mithro/esp32-to-433mhz/firmware/docs/esp32c3-cc1101-node.md

# ESP32-C3 SuperMini + CC1101 — Tasmota 433 MHz node

**Status (2026-09-05):** design + host-tested decoders + bench tooling; the
Tasmota firmware is the overlay in `firmware/` (Plan B). On-hardware validation of
the radio foundation (detect / register-I/O / selection) and the CC1101 OOK
edge-capture path is recorded in [`HWTEST-RESULTS-cc1101.md`](HWTEST-RESULTS-cc1101.md);
bench captures of the remotes/Merlin are still pending a human at the bench.

A small WiFi/USB 433 MHz transceiver: an **ESP32-C3 SuperMini** driving a
**D-SUN CC1101** SPI module (or an Ebyte E07-M1101D, or an SX1278 RA-02), running
Tasmota with a custom CC1101/SX1278 driver. It receives the Fineoffset weather
stations (FSK) — now confirmed decoding live on both a CC1101 node and the
SX1278 — and, **implemented in firmware and host-tested but not yet verified
on air**, receives the OOK-PWM remotes and the Merlin garage remote and
transmits OOK (`CcRfSend`) and Security+ 2.0. It publishes rtl_433-shaped
JSON + `RfReceived` to MQTT (and the same over its native-USB console).

> **Scope note.** The consolidated firmware in `firmware/` builds the radio
> *foundation* (detect / register-I/O / radio selection), the CC1101 OOK + FSK
> weather + decoder functionality, and the **SX1278 (RA-02) Fine Offset FSK
> receive path** (weather parity with the CC1101 — see the section below). The
> SX1278 FSK **transmit** is now implemented and **confirmed on-air** (15/15 independent
> decode at +2 dBm, see below). SX1278 OOK TX and OOK/LoRa RX are
> still future work (OOK-continuous
> RX also needs a DIO2 wire this adapter does not route); `sx1278_radio.cpp`
> currently implements only the Fine Offset FSK-RX path.

The board carrier/adapter (KiCad) and the full design spec live elsewhere: the
KiCad adapter is this repo's top-level [`README.md`](../../README.md) and
`hardware/`; the design spec and the numbered rulings (R1-R8) are in the project
repo (github.com/mithro/433mhz, `docs/.../2026-08-20-esp32c3-cc1101-tasmota-design.md`).

## Radio capability matrix

One firmware binary (`tasmota32c3-cc1101.bin`) runs on every node regardless of
which radio is fitted; `Radio auto|cc1101|sx1278` selects the active radio at
boot and the Tasmota template assigns the physical pins — there is no separate build
per radio family. (Board-type-strap auto-detection is implemented but was not exercised
on hardware; every on-hardware session used explicit `Radio cc1101`/`sx1278`.)

The two radio families are **not** at full functional parity, by design/hardware
constraint rather than by an unclosed code gap:

| Capability | CC1101 (blue E07 / green D-SUN) | SX1278 (Ra-02) |
|---|---|---|
| Fine Offset FSK RX (WS69/WH65B, WH51) | Yes | Yes — same `fineoffset_decode()` decoder as the CC1101 path |
| Fine Offset FSK RX (WS85, >=28 B frame) | **Not over-air** — the frame exceeds the CC1101's 25-byte fixed packet, so the WS85 branch is unreachable on this RX path (decoder host-tested only) | Fits the 30-byte packet (host-tested only; no WS85 sensor on air at the site) |
| OOK-PWM remote RX | Edge-capture/ISR live on hardware; a clean live OOK **remote decode** is not yet confirmed on air | **No** — OOK-continuous RX needs the SX127x **DIO2/DATA** pin, which this RA-02 adapter does not route |
| Security+ 2.0 (rolling-code garage remote) | Yes — built on the OOK-PWM RX path | **No** — depends on OOK-PWM RX, which this radio does not have on this adapter |
| OOK / Security+ 2.0 TX | Yes — template-driven pins, one firmware binary (`CcRfSend`, `SecplusSend`) | **No** — OOK TX needs the DIO2 line this adapter does not route |
| Fine Offset 2-FSK TX | No (this radio does OOK TX only) | **Yes** — `SxFskTx`, confirmed on-air (15/15 independent decode) |
| Register I/O, reset, radio selection | Yes | Yes |

**Live-hardware status (updated 2026-09-06)** (host-tested/build-verified is not the
same claim as confirmed decoding on real silicon — kept separate here):
- CC1101 blue: the OOK-PWM edge-capture path is live-verified on hardware
  (see [`HWTEST-RESULTS-cc1101.md`](HWTEST-RESULTS-cc1101.md)). green's edge-capture only
  ran via host-mediated (USB) resets; green does **not** run its app from a cold power-on
  (it boots ROM download — see the HWTEST green section), so only blue is a proven-working
  CC1101. Fine Offset FSK RX
  (WS69/WH51) is now **confirmed decoding live on CC1101 hardware** on blue,
  after the 2026-09-06 RX-bandwidth fix (MDMCFG4 `0xC9` -> `0x59`, 101 kHz ->
  325 kHz — the narrow filter could not cover the module crystal's frequency
  offset). The earlier `Decoded=0` runs predate that fix; blue's live decode, and
  the real-broker HA verification, are recorded in
  [`HWTEST-RESULTS-cc1101.md`](HWTEST-RESULTS-cc1101.md).
- SX1278 (Ra-02): Fine Offset FSK RX is both host-tested and **confirmed decoding
  live on hardware** (WS69 id 174, WH51 id 0f5d66, cross-checked against the rpi5
  reference; recorded in [`HWTEST-RESULTS-cc1101.md`](HWTEST-RESULTS-cc1101.md)).
- OOK/Security+ 2.0 TX is host-tested and build-verified but has not yet been
  exercised end-to-end against a real receiver.

[`sx1278_radio.cpp`](../src/cc1101_node/sx1278_radio.cpp) currently implements the
SX1278's Fine Offset FSK-RX path only; FSK/OOK TX, OOK-RX and LoRa are future work
(see the capability notes above).

## Wiring

The wiring diagram is generated by [`../tools/esp32c3-cc1101-node-wiring.py`](../tools/esp32c3-cc1101-node-wiring.py)
(its `WIRES` table is the single source of truth, checked by `tests/test_common.py`).

| D-SUN pin | ESP32-C3 GPIO | Role | Why |
|---|---|---|---|
| VCC | 3V3 | 3.3 V supply (~35 mA peak in TX) — **never 5 V** | SuperMini LDO is adequate |
| GND | GND | | |
| SCK | GPIO4 | SPI clock | Arduino-core FSPI default |
| MOSI (SI) | GPIO6 | SPI -> CC1101 | FSPI default |
| MISO (SO) | GPIO5 | SPI <- CC1101 (also CHIP_RDYn while CS low) | FSPI default |
| CSN | GPIO7 | chip select | FSPI default |
| GDO0 | GPIO3 | FSK: packet-ready IRQ; OOK: **TX data in** (RMT out) | no boot role |
| GDO2 | GPIO10 | OOK: **RX demod data out** (RMT capture in); FSK: spare status | no boot role |

**Do not use** GPIO2/8/9 (strapping; 8 is the blue LED, 9 is BOOT), GPIO20/21
(UART0, kept free as a fallback console), GPIO18/19 (USB D-/D+). After reset
GDO0 outputs CLK_XOSC/192 until configured — harmless on GPIO3. The D-SUN
header is 2x4; pin names as on its silkscreen: (VCC GND) (SCK MOSI) (GDO2 MISO)
(CSN GDO0). The SuperMini's PCB WiFi antenna is marginal: placement matters.

Per-board pin maps (blue E07, green D-SUN, SX1278 RA-02) that the firmware
probes at boot are tabulated in [`../README.md`](../README.md) -> *Radio
selection and SX1278 (RA-02) support*.

### Tasmota template
`GPIO4=SPI CLK, GPIO5=SPI MISO, GPIO6=SPI MOSI, GPIO7=CC1101 CS, GPIO3=CC1101 GDO0, GPIO10=CC1101 GDO2`, then `Module 0`.
See [`../README.md`](../README.md) -> *Commissioning a node* for the exact raw
`Template` array (the GDO pin functions are gated behind `USE_KEELOQ` upstream,
so only the raw array assigns them in this build).

### Reference setup on rpi5-433mhz (direct SPI, no ESP)

| D-SUN | Pi 5 header | BCM |
|---|---|---|
| VCC | pin 1 | 3V3 |
| GND | pin 6 | GND |
| SCK | pin 23 | GPIO11 SCLK |
| MOSI | pin 19 | GPIO10 MOSI |
| MISO | pin 21 | GPIO9 MISO |
| CSN | pin 24 | GPIO8 CE0 (`/dev/spidev0.0`) |
| GDO2 | pin 18 | GPIO24 — **black** wire (OOK capture, [`../tools/cc1101_ook_capture.py`](../tools/cc1101_ook_capture.py) `--gpio 24`) |
| GDO0 | pin 22 | GPIO25 — **green** wire (reserved for async TX tests) |

GDO assignment measured 2026-08-22 with [`../tools/cc1101_find_gdo_pins.py`](../tools/cc1101_find_gdo_pins.py)
(drives each GDO to a fixed level and scans the header: `GDO2 -> GPIO24 (header
pin 18)`, `GDO0 -> GPIO25 (header pin 22)`); wire colours as recorded by Tim.
The 3V3/GND pin numbers are the conventional choice, not measured. The Pi-side
reference driver is [`../tools/cc1101.py`](../tools/cc1101.py), which the firmware
presets are proven against (`tests/test_presets.py`).

## Bill of materials (9 units)
ESP32-C3 SuperMini x9 · D-SUN CC1101 433 MHz module with antenna x9 ·
8-way female-female jumper sets or a 2x4 + 2x8 header adapter x9 · USB-C cable
and 5 V supply per deployed node.

## Modes, commands, MQTT

All commands are issued on the Tasmota console or over MQTT as
`cmnd/<topic>/<Command> [args]`, replying on `stat/<topic>/RESULT`. Config-setting
commands persist to `/cc1101.cfg`. For the full per-field MQTT message schema, the
Home Assistant autodiscovery setup (the `rtl433-mqtt-autodiscovery` add-on on
`rtl_433/+/events`), the `CcHass` events-topic option, node MQTT configuration and
the live-broker validation procedure, see
[`mqtt-home-assistant.md`](mqtt-home-assistant.md).

### Command reference

**Radio selection and mode**

| Command | Args | Description |
|---|---|---|
| `Radio` | `auto\|cc1101\|sx1278` | Select and persist the active radio engine; re-runs bring-up. |
| `CcMode` | `weather\|remotes` | CC1101 role: Fine Offset FSK RX (`weather`) or OOK-PWM remotes RX (`remotes`). Persisted. |

**CC1101**

| Command | Args | Description |
|---|---|---|
| `CcStatus` | - | Present, PARTNUM/VERSION/MARCSTATE, mode/preset, RSSI, Rx/Decoded/Tx/Overflow counters. |
| `CcPreset` | `<name>` | Load a named preset and enter RX (debug). |
| `CcReg` | `<addr> [val]` | Read/write a CC1101 register (0x00-0x3F; writing 0x30-0x3D issues a strobe). |
| `CcRaw` | `0\|1` | Publish drained-but-undecodable frames as hex on `tele/<topic>/CCRAW`. |
| `CcHass` | `0\|1` | Events topic layout: `0` = `rtl_433/nodes/<host>/events` (aggregator), `1` = `rtl_433/<host>/events` (direct HA autodiscovery). |
| `CcRfSend` | `{"Data","Bits","Protocol":1,"Pulse","Repeat"}` | Transmit an OOK-PWM (RCSwitch protocol 1) code. |
| `CcTxPower` | `[byte]` | CC1101 OOK **mark** level = `PATABLE[1]` (`0` = preset default; e.g. `0xC0` ~ +10 dBm at 433 MHz). Space stays `PATABLE[0]=0x00`. |
| `CcRxGain` | `[byte]` | CC1101 `AGCCTRL2` (0x1B) RX-gain override (`0` = preset default; lower `MAX_LNA/DVGA_GAIN` reduces sensitivity for a strong co-located source). |

**SX1278 (RA-02)**

| Command | Args | Description |
|---|---|---|
| `SxStatus` | - | Present, VERSION, Active, Mode, WeatherRx, RSSI, Rx/Decoded/Tx. |
| `SxReg` | `<addr> [val]` | Read/write an SX127x register (address bit7 = write). SX1278 must be the active radio. |
| `SxReset` | - | Hardware reset (RST pulse) and re-identify. |
| `SxFskTx` | `<hex>` | Transmit the hex payload as a fixed-length 2-FSK packet matched to the RX preset (433.92 MHz, 17.241 kbps, sync 0x2DD4). |
| `SxTxPower` | `[2..17]` | SX1278 PA_BOOST output power in dBm (`0` = default +17). |
| `SxRxGain` | `[1..6]` | SX1278 LNA gain (`1` = max G1 .. `6` = min G6; `0` = AGC-auto default). |

**Security+ 2.0** (CC1101 only)

| Command | Args | Description |
|---|---|---|
| `SecplusId` | `[id]` | Get/set the persisted Security+ 2.0 device id. |
| `SecplusCounter` | `[n]` | Get/set the rolling counter (persisted before each keying). |
| `SecplusFreq` | `[f1 f2 f3]` | Get/set the frequency legs (default 433.92). |
| `SecplusSend` | - | Transmit a Security+ 2.0 rolling-code frame. |

> Note: `SxFskTx` and `SxTxPower`/`SxRxGain` (and the CC1101 `CcTxPower`/`CcRxGain`)
> are the runtime power/TX controls added for co-located on-air testing -- reduce
> TX power (or RX gain) so a nearby receiver is not desensitised.

## Decoders and fixtures (host-tested)
`../decoders/` — Fineoffset WS69/WH65B/WS85/**WH51** (soil moisture, family 0x51) and OOK-PWM in pure C, tested with
`uv run --with pytest pytest firmware/tests` against real captures in
`../fixtures/`. rtl_433 field names throughout. The bit-sense convention of the
OOK-PWM codes is documented in the project repo's `protocols/ook-pwm-remotes.md`.

## Fine Offset FSK RX configuration and packet-length handling

The `fineoffset-fsk` preset (`../src/cc1101_node/cc1101_presets.c`) programs the
CC1101 like the bench-proven reference `cc1101_watch.py`
(`configure_fineoffset_fsk_rx`), computed from the datasheet formulas, with one
deliberate deviation: the RX bandwidth is widened from the reference's 101 kHz to
**325 kHz** (MDMCFG4 `0xC9` -> `0x59`) so the filter covers the module crystal's
frequency offset (2026-09-06 fix; see `cc1101_presets.c`). Every other register
was read back from a live node (`CcReg`) and matches the reference:

| Purpose | Register(s) | Value |
|---|---|---|
| Carrier 433.92 MHz | FREQ2/1/0 (0x0D/0E/0F) | `10 B0 71` |
| Bit rate 17.24 kbps | MDMCFG4/3 (0x10/0x11) | `59 5C` |
| 2-FSK, 16/16 sync, no Manchester | MDMCFG2 (0x12) | `02` |
| 24-byte preamble | MDMCFG1 (0x13) | `72` |
| Deviation 50 kHz | DEVIATN (0x15) | `50` |
| Sync word 0x2DD4 | SYNC1/0 (0x04/0x05) | `2D D4` |
| Fixed length, APPEND_STATUS, no CRC autoflush | PKTCTRL0/1 (0x08/0x07) | `00` / `04` |
| Channel BW 325 kHz | (in MDMCFG4) | — |

**Packet length — receiving both WS69 (25 B) and WH51 (14 B).** The CC1101 runs a
fixed-length packet (`CC_FSK_PKTLEN = 25`, sized to the WS69/WH65B frame, whose
tail CRC needs all 25 bytes). `CcWeatherPoll()` accepts a *range* of Fine Offset
frame lengths so the shorter WH51 is also captured and dispatched:

- **Full-packet path** (`RXBYTES >= PKTLEN + 2`): reads the completed 25-byte
  packet plus its 2 appended status bytes and calls `fineoffset_decode()`, which
  dispatches by the family byte — `0x24` -> WS69/WH65B, `0x51` -> WH51,
  `0x85` -> WS85. A 14-byte WH51 arrives in the first 14 bytes with the rest of
  the packet filled by demodulated bytes; the decoder ignores everything past the
  14-byte frame (validated by CRC-8 poly 0x31 + additive checksum), so it decodes
  correctly inside the longer read.
- **Short-frame rescue** (`RXBYTES >= 14` and the FIFO has stopped growing):
  drains a WH51 whose packet stalled before completing 25 bytes, and decodes it
  **only when it starts with the WH51 family byte 0x51** — so a partially-filled
  WS69/WS85 (both arrive in one <=12 ms burst, faster than the 50 ms poll) can
  never be truncated into a false decode.

**WS85 is not audible at Welland.** A WS85 frame is >=28 bytes — longer than the
fixed 25-byte packet — so its decode branch is unreachable on this RX path and no
WS85 was heard on air during the 2026-09-05 survey. WS85 (family 0x85) is
therefore validated by the decoder host test (real rtl_433 doc vector) only — Renode's
cc1101_decode suite runs WS69+WH51, not WS85 — and not by a live capture. Raising `CC_FSK_PKTLEN` to fit WS85 would stop the CC1101
completing the shorter WS69 frame, so it is left at 25.

## SX1278 (RA-02) Fine Offset FSK RX configuration

The SX1278 receives the same Fine Offset families as the CC1101 weather path
(`../src/cc1101_node/sx1278_radio.cpp`, `configure_fineoffset_fsk()`). Every value
is computed from the SX1276/78 datasheet formulas and matched to the bench-proven
SX1276 receiver at the same Welland site (rpi5 `~/wh51-watch`, RadioLib
`beginFSK`: 433.92 MHz, 17.241 kbps, ~50 kHz fdev, sync `0x2DD4`, 2-FSK with
`ModulationShaping = NONE`):

| Purpose | Register(s) | Value |
|---|---|---|
| FSK mode (LongRangeMode=0), low-freq band, RX | RegOpMode (0x01) | `0D` |
| Carrier 433.92 MHz (`Frf = Fstep·RegFrf`, Fstep = 32 MHz/2¹⁹) | RegFrf (0x06/07/08) | `6C 7A E1` |
| Bit rate 17.241 kbps (`FXOSC / RegBitrate`) | RegBitrate (0x02/03) | `07 40` |
| Deviation ~50 kHz (`Fstep · RegFdev`) | RegFdev (0x04/05) | `03 33` |
| RX bandwidth 125 kHz (mant=16, exp=2) | RegRxBw (0x12) | `02` |
| AGC auto + RX trigger on preamble detect | RegRxConfig (0x0D) | `0E` |
| Preamble detector on, 2 bytes, tol 10 | RegPreambleDetect (0x1F) | `AA` |
| AutoRestartRx + SyncOn + 2 sync bytes (0xAA preamble polarity) | RegSyncConfig (0x27) | `91` |
| Sync word 0x2DD4 | RegSyncValue1/2 (0x28/29) | `2D D4` |
| Fixed length, no DC-free, no CRC, no addr filter | RegPacketConfig1 (0x30) | `00` |
| Packet (not continuous) data mode | RegPacketConfig2 (0x31) | `40` |
| Fixed payload length = `SX_FSK_RX_LEN` (30) | RegPayloadLength (0x32) | `1E` |
| DIO0 = PayloadReady (also polled via RegIrqFlags2) | RegDioMapping1 (0x40) | `00` |

**Packet length — one config for every family.** Unlike the CC1101's 25-byte
fixed packet + short-frame rescue, the SX1278 runs **fixed-length packet mode with
`RegPayloadLength = SX_FSK_RX_LEN = 30`** — chosen `>=` the longest WS85 frame
(28 B) yet `<=` the 64-byte FIFO. After the demodulator matches `0x2DD4`, the radio
latches 30 bytes into the FIFO and raises **PayloadReady**; `sx_weather_drain()`
(`../src/cc1101_node/sx1278_weather.cpp`) reads all 30 out of `RegFifo` and
`fineoffset_decode()` dispatches by family byte (`0x24` WS69/WH65B, `0x51` WH51,
`0x85` WS85), ignoring the trailing demodulator noise that follows a short frame.
So **one** setting receives WH51 (14 B), WS69 (25 B) and WS85 (28 B) — the SX1278
does not need the CC1101's split full-packet/short-frame logic because 30 bytes
always fits every family and the decoder self-selects by length. Because 30 <= 64
the frame never straddles a FIFO refill. After each drain the driver does a
`standby -> RX` (`restart_rx()`) — belt-and-suspenders alongside AutoRestartRx —
to flush the FIFO and re-arm sync detection.

`SX_FSK_MIN_FRAME` is 14 (WH51); anything the decoder rejects is optionally
published as raw hex over `tele/…/CCRAW` when `CcRaw 1` is set. The SX1278 does
**weather RX only**: OOK-continuous "remotes" RX needs the SX127x DIO2 data line,
which this RA-02 adapter does not route, so `CcMode remotes` leaves the SX1278 in
standby.

Host-tested end to end by `../tests/test_sx1278_weather_rx.py`, which drives the
identical `sx_weather_drain()` through a scripted FIFO for WH51/WS69/WS85 and
asserts the config registers above against the datasheet math.

## SX1278 (RA-02) Fine Offset FSK transmit

`SxFskTx <hex>` transmits the payload as a fixed-length 2-FSK packet through the SX1278 (which
must be the active radio, `Radio sx1278`). The TX preset (`configure_fsk_tx()`) uses the
**same** carrier / bit-rate / deviation / sync as the RX preset (433.92 MHz, 17.241 kbps,
~50 kHz fdev, 0xAA preamble + 0x2DD4 sync), so a peer running the CC1101 `FINEOFFSET_FSK`
preset -- or another SX1278 in weather RX -- is on-air compatible. The command pauses weather
RX, loads the FIFO, keys the transmitter (PA_BOOST, +17 dBm), waits for the `PacketSent` IRQ
(with a timeout), then re-arms RX; `SxStatus` reports a `Tx` counter.

**OOK TX is not provided:** like OOK RX, arbitrary OOK-PWM transmit needs the SX127x
continuous-mode DATA line (DIO2), which the RA-02 socket does not route (`SX_MAP_RA02` wires
only DIO0). FSK *packet* TX drives the FIFO over SPI and works on the wiring as built.

**Validation state (2026-09-08):** host-tested (SPI framing, FIFO burst-write order, and TX
modem params asserted equal to the RX preset -- `../tests/test_sx1278_fake_bus.py`) **and
confirmed on-air.** The transmit was received and decoded by an INDEPENDENT receiver -- the
rpi5-SPI CC1101 (`~/wh51-watch/cc1101_watch.py`, a different chip and a different decoder
codebase than this firmware): a 15-frame burst of the WH51 fixture at **+2 dBm** (`SxTxPower 2`)
produced 15/15 decodes of id `0f5c54` at RSSI -41 dBm (vs the real sensor's -73..-88 dBm; a
rapid cluster impossible for the ~70 s-interval real sensor). At the default +17 dBm the
co-located receiver was desensitised and decoded nothing -- the runtime `SxTxPower` control
(and `CcTxPower`/`SxRxGain`/`CcRxGain`) exists precisely for co-located on-air tests. This is
both an on-air TX confirmation and an independent-oracle cross-check of the node's output.

## Why these choices (so they aren't relitigated)
- **Why RMT:** the C3's RMT peripheral timestamps edges in hardware (1 us) and
  buffers them; WiFi/MQTT cannot jitter pulse measurement; the same peripheral
  generates exact TX pulse trains, which Security+ 2.0 needs.
- **Why two GDOs:** packet mode (FSK) wants an IRQ on GDO0; async-serial mode
  (OOK) wants RX data on GDO2 and TX data on GDO0. The D-SUN has both.
- **Why not ESPHome/Berry:** estate and HA are Tasmota; stock Tasmota has no
  CC1101 driver and Berry has no SPI/RMT — see the design spec section 2.
- **FSK vs OOK exclusivity:** a CC1101 does one at a time; nodes get a role
  (`CcMode weather|remotes`).

## Verification log
| Date | Check | Result (command output) |
|---|---|---|
| 2026-08-20 | WS69 id 174 25-byte frames on Pi CC1101 (`cc1101_ws69_rx.py --packet-len 25`) | `24 AE 5D 82 13 52 05 01 07 24 00 00 00 00 00 5A A1 01 FF FF FF 01 6B 87 33` twice at 16 s, RSSI -85.5/-87.0 dBm; both CRCs valid; decodes 13.1 C 82 % 349 deg 464.3 mm |
| 2026-08-22 | async-OOK capture path: GDO2->GPIO24 (measured with `cc1101_find_gdo_pins.py`); no-remote baseline — `MARCSTATE=0x0D`, `edges=48 trains(>=16 pulses)=0` over 10 s — path live end-to-end. Remote captures vs the codes doc, and rtl_433 cross-check: **PENDING — needs a human at the Welland bench** |
| 2026-09-05 | Tasmota firmware on real CC1101 (blue E07 + green D-SUN), native-USB console: PARTNUM 0x00 / VERSION 0x14, register I/O, radio selection, OOK edge-capture live; SX1278 RA-02 RegVersion 0x12 detect + register-I/O + selection | See [`HWTEST-RESULTS-cc1101.md`](HWTEST-RESULTS-cc1101.md) |
| 2026-09-05 | WH51 decoder: real frame `51 0F 5C 54 10 7F 28 F8 D0 FF FF FF 4B D7` (id 0f5c54) captured by the rpi5 reference logger; host test asserts moisture 40, battery 1600 mV, ad_raw 208, battery_ok 1.0 vs rtl_433 -> **108 host tests pass** (as of this 2026-09-05 entry; the suite is now 146 tests) | `pytest firmware/tests` |
| 2026-09-05 | WH51 live on a node CC1101: **NOT decoded.** blue (E07) + green (D-SUN) in `weather` mode received strong 433.92 FSK traffic (RSSI down to -26 dBm) and completed packets (`Rx` climbing), but never a WH51 frame (`Decoded=0`); registers directly comparable to the proven reference read back identical, PKTLEN 25->17 tried, sync relaxed 16/16->15/16 (`Rx` 376 in 90 s, still `Decoded=0`). The reference CC1101/LilyGo on rpi5 heard the same WH51 sensors at -74..-82 dBm throughout. Cause not isolated in this run (a packet-framing config bug — fixed-length vs. infinite-length mode — was found afterward; whether that explains this result is unproven on this hardware, since PKTLEN=17 was also tried here and still did not decode). **Superseded (2026-09-06):** the cause was RX bandwidth — MDMCFG4 `0xC9` (101 kHz) is too narrow for the module crystal's frequency offset; widening it to `0x59` (325 kHz) made blue decode WS69+WH51 live (recorded in the on-hardware results log). | reference `cc1101.hits.jsonl` vs node console |
| 2026-09-05 | **SX1278 (RA-02) FSK weather RX — LIVE, decoded.** Node MAC 44:1B:F6:2E:B3:80 (`/dev/radio-sx1278-ra02`) flashed with this build, `Radio sx1278` + `CcMode weather`: `SxStatus` -> `Present 1, VERSION 0x12, WeatherRx 1`; console `RSL: events` lines decoded **WS69 id=174** (humidity 79, `mic:CRC`) repeatedly at RSSI -89..-93 dBm and **WH51 id=0f5d66** (moisture 38, `mic:CRC`), i.e. both families through the single fixed-length FSK config. Cross-checked against the rpi5 reference (`~/wh51-watch`) for the same window: reference heard WS69 family 0x24 id 0xAE(174) humidity 0x4F(79) and WH51 id 0f5c54 valid at -82 dBm. Float fields render as `*float*` on-target (shared-decoder `%f` under newlib-nano, affects the CC1101 path identically — not radio-specific; integer fields + CRC MIC correct). | node console vs `cc1101.hits.jsonl`/`lilygo.jsonl` |
| 2026-08-22 | Merlin remote: rtl_433 -R 164 / 178 / -A | **PENDING — needs a human to press the remote**; procedure in the project repo's `protocols/secplus-v2.md` |
| 2026-09-05 | **FIX-A: SX1278 (RA-02) re-capture with the `rf_ftoa` float fix (`4c85365`), valid floats confirmed + 3-way cross-check.** Single reflash from HEAD `cd95b48` (`firmware/dist/tasmota32c3-cc1101.factory.bin`, sha256 `9c933635b5...`), `esptool write_flash 0x0`, hash-verified; commissioned `Radio sx1278` (weather RX already persisted from the WAVE A2 session). 10-minute passive console capture over a persistent `dtr=False,rts=False` connection, 2026-09-05T12:53:39-13:03:39 UTC. `events` JSON now carries real numeric floats end to end, e.g. `{"model":"Fineoffset-WS69","id":174,"battery_ok":1,"temperature_C":13.0,"humidity":84,"wind_dir_deg":8,"wind_avg_m_s":0.4,"wind_max_m_s":0.5,"rain_mm":517.7,"uv":0,"uvi":0,"light_lux":0.0,"mic":"CRC"}` and `{"model":"Fineoffset-WH51","id":"0f5c54","battery_ok":1.0,"battery_mV":1600,"moisture":40,"boost":0,"ad_raw":208,"mic":"CRC"}` - **no `*float*` anywhere in the 10-minute capture** (previously reported bug from WAVE A2 is fixed). **Cross-check:** (1) WH51 **target id `0f5c54`** (previously below the CC1101-node SNR budget) decoded by the node at 13:03:36.354 UTC matches, byte-for-byte on the 14-byte payload (`51 0F 5C 54 10 7F 28 F8 D0 FF FF FF 4B D7`), the rpi5 reference CC1101 logger (`cc1101.hits.jsonl`, ts 13:03:36.048) **and** the LilyGo SX1276 logger (`lilygo.hits.jsonl`, ts 13:03:36.053) - moisture 40, battery 1600 mV, ad_raw 208 on all three receivers. (2) WS69 id=174 events at 12:53:59.446/12:54:31.279 UTC match the LilyGo raw frames (`24 AE 08 ...`/`24 AE 0B ...`) byte-for-byte on the shared payload, decoding to identical temperature_C 13.0, humidity 84, wind_dir_deg 8, wind_avg_m_s 0.4, wind_max_m_s 0.5, rain_mm 517.7. (3) Pluto SDR (`rpi-sdr-pluto`, `rtl_433 -d driver=plutosdr`): its pre-existing continuous logger (running unattended since 2026-09-02) had already stopped producing new decodes before this session started (last flush recorded, per its own drifting internal clock, `"time":"2026-09-05T13:44:32"`, `rain_mm:517.144` = 2 tip-counts / 0.5 mm behind the node/reference's `517.7`, i.e. genuinely stale, not futuristic) - it continues to independently confirm the same on-air WS69 id=174 (same battery_ok, same rain-counter epoch) but not from inside this session's exact 10-minute window. Two restarts (its own auto-restart wrapper) reconnected to the Pluto cleanly (no USB claim errors) but did not resume live decoding within this session's time budget - an infra/logging-tool staleness issue on a *pre-existing, unattended* capture tool, not a fault in the node/firmware under test or in the Pluto radio itself. **Node stayed healthy** throughout (single flash, no further reflash); one console reconnect for a post-capture `SxStatus` check reset the RAM counters only (config/mode persisted) - the same known reconnect-resets-C3 bench-harness gotcha already documented above. | node console (`a2recap-node-console.log`) vs `cc1101.hits.jsonl`/`lilygo.hits.jsonl`/pluto `rtl433.jsonl` |

## See also
- [`../README.md`](../README.md) — firmware build, flashing, commissioning, command reference, MQTT.
- [`../RECOVERY.md`](../RECOVERY.md) — reflashing a bricked/misbehaving board, restoring `/cc1101.cfg`.
- [`HWTEST-RESULTS-cc1101.md`](HWTEST-RESULTS-cc1101.md) — on-hardware validation log.
