mithro/esp32-to-433mhz/hardware/parts/sx1278-ra02-breakout/photos/ra02-header.jpg

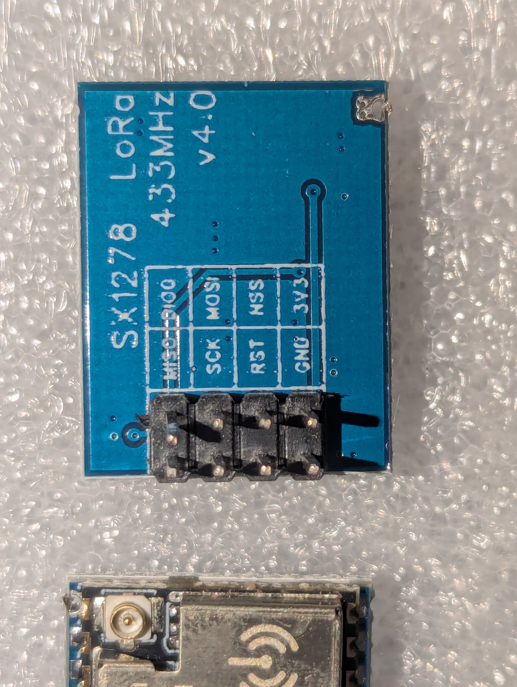
hardware/parts/sx1278-ra02-breakout/photos/ra02-header.jpg
