mithro/esp32-to-433mhz/hardware/3d/cc1101-dsun.step

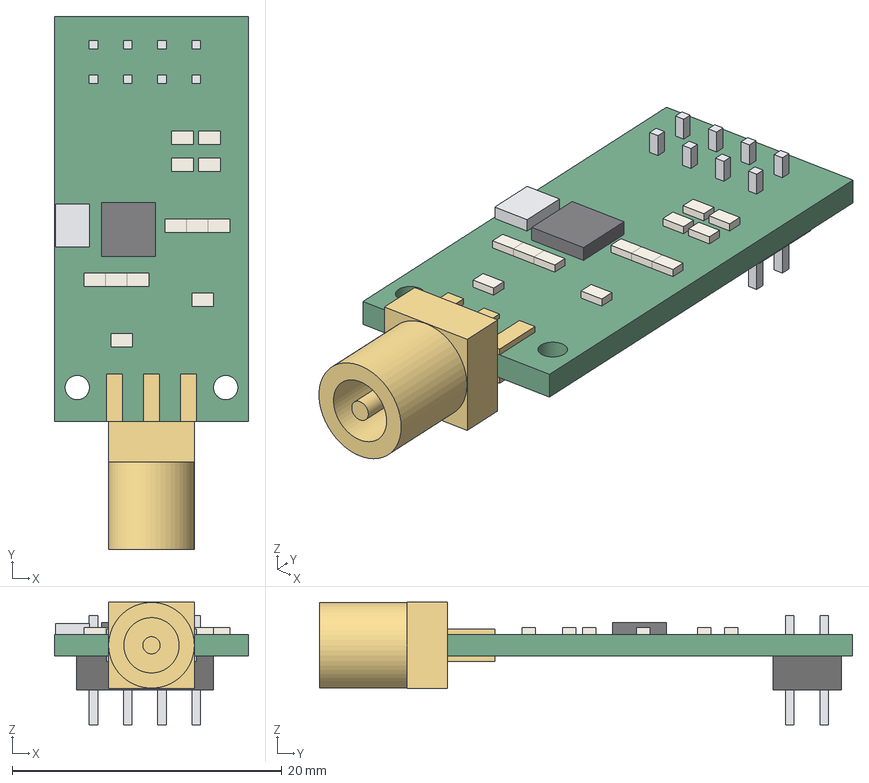
[picture p60: CAD file, 2026-09-10]
hardware/3d/cc1101-dsun.step
14.4 x 39.5 x 9.10 mm
pcb_0
cc1101_1
crystal_2
passive_3
passive_4
passive_5
passive_6
passive_7
passive_8
passive_9
passive_10
passive_11
passive_12
passive_13
passive_14
sma_body_15
sma_pin_16
sma_leg_17
sma_leg_18
sma_leg_19
sma_leg_20
sma_leg_21
pins_23
