mithro/esp32-to-433mhz/hardware/3d/esp32-c3-supermini-components.step

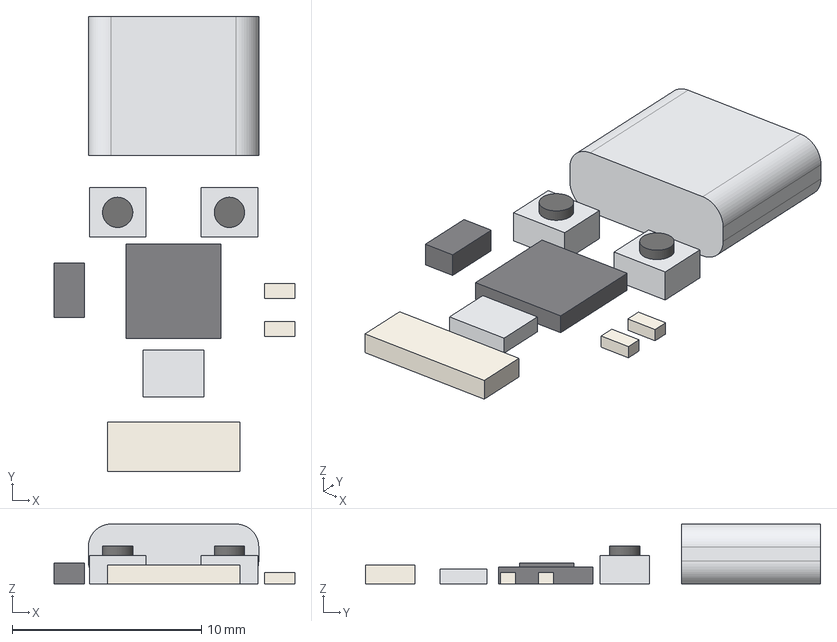
[picture p61: CAD file, 2026-09-10]
hardware/3d/esp32-c3-supermini-components.step
12.7 x 24.0 x 3.16 mm
usb_c_0
button_1
button_cap_2
button_3
button_cap_4
esp32c3_5
crystal_6
ldo_7
led_8
led_9
antenna_10
