mithro/esp32-to-433mhz/hardware/3d/cc1101-dsun-components.step

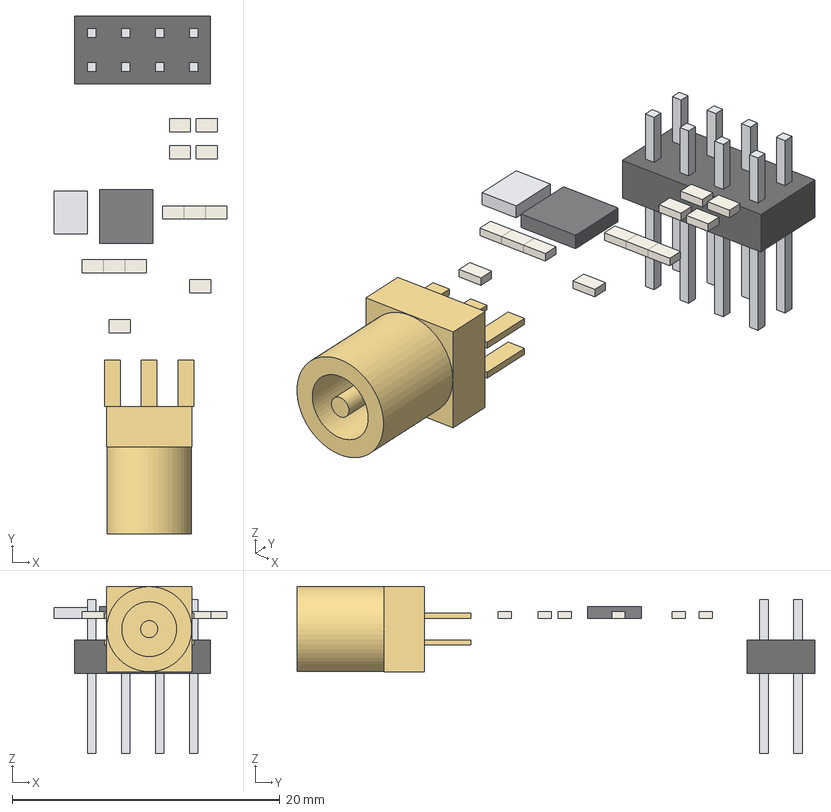
[picture p62: CAD file, 2026-09-10]
hardware/3d/cc1101-dsun-components.step
12.9 x 38.7 x 12.5 mm
cc1101_0
crystal_1
passive_2
passive_3
passive_4
passive_5
passive_6
passive_7
passive_8
passive_9
passive_10
passive_11
passive_12
passive_13
sma_body_14
sma_pin_15
sma_leg_16
sma_leg_17
sma_leg_18
sma_leg_19
sma_leg_20
pins_22
