mithro/esp32-to-433mhz/hardware/3d/sx1278-ra02-pigtail.step

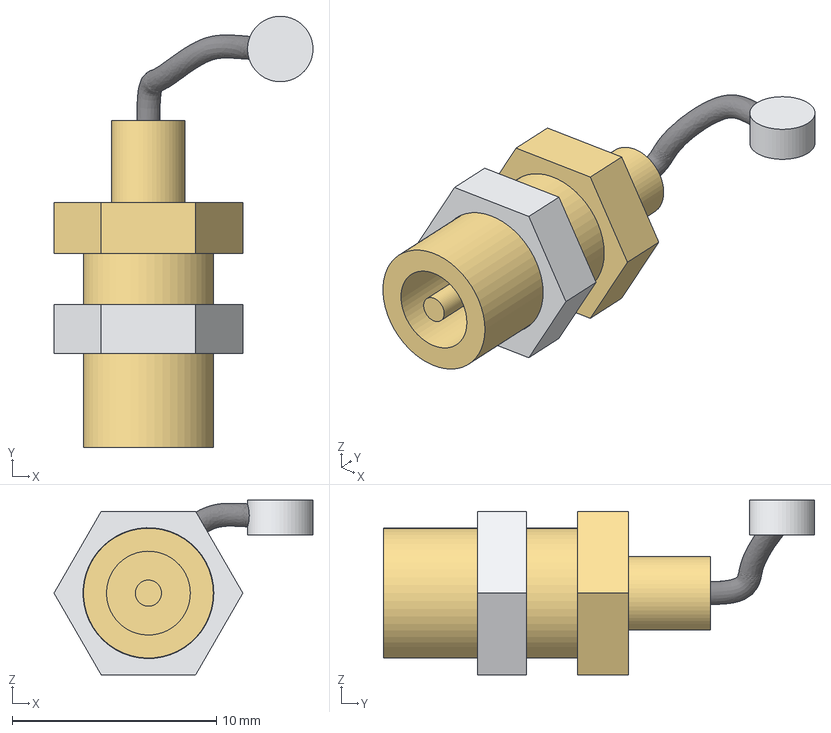
[picture p63: CAD file, 2026-09-10]
hardware/3d/sx1278-ra02-pigtail.step
12.7 x 21.1 x 8.55 mm
ufl_plug_0
cable_1
sma_bulkhead_2
sma_pin_3
sma_nut_4
