mithro/esp32-to-433mhz/docs/images/esp32c3-radio-adapter-assembly-e07-top.png

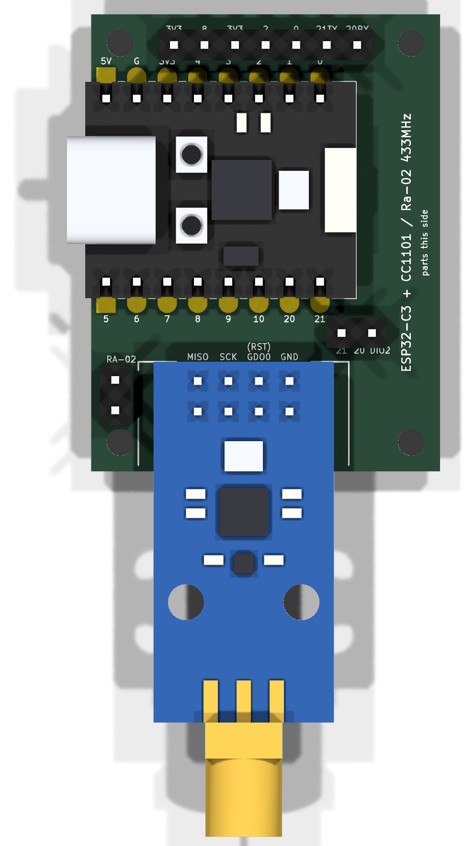
docs/images/esp32c3-radio-adapter-assembly-e07-top.png
