mithro/esp32-to-433mhz/docs/images/esp32c3-sx1278-adapter-assembly-module-top.png

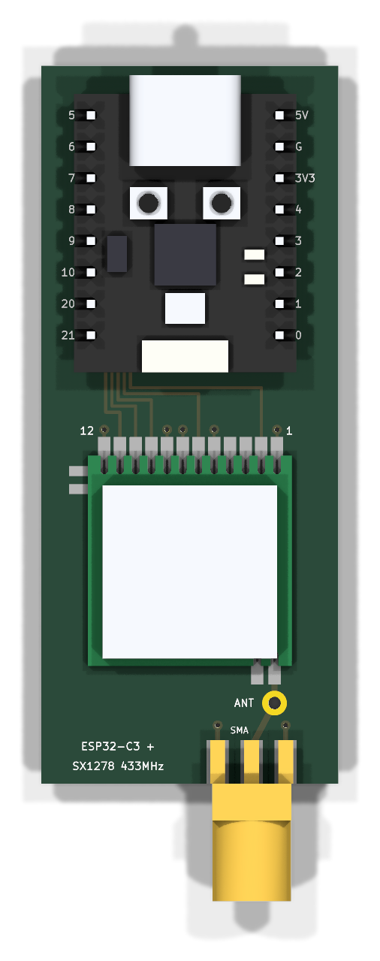
docs/images/esp32c3-sx1278-adapter-assembly-module-top.png
