mithro/esp32-to-433mhz/scripts/generate_adapters.py

#!/usr/bin/env -S uv run --script
# /// script
# requires-python = ">=3.11"
# dependencies = []
# ///
"""Generate two small carrier boards that connect an ESP32-C3 SuperMini to a
433 MHz radio module:

* hardware/esp32c3-sx1278-adapter  - SuperMini + the 16-pin castellated
  SX1278 LoRa module (soldered onto SMD land pads) + a hole for the spring
  antenna wire.  Two-layer; the SuperMini sits at the top with its USB-C
  pointing off the top edge and its pins in 1.0 mm through-holes.
* hardware/esp32c3-radio-adapter   - SuperMini + one 2x4 socket that takes
  either the Ebyte E07-M1101D-SMA CC1101 board or the "SX1278 LoRa 433MHz
  v4.0" Ra-02 breakout (their headers differ in only two positions).  Every
  track on B.Cu, GND pour on F.Cu, silk on both sides, M2 holes in the
  corners.  The SuperMini lies on its side with its USB-C hanging off the
  left edge; its pins land on keyhole pads (1.0 mm hole plus copper extended
  past the SuperMini's edge) so it can be fitted with header pins or
  soldered flat by its castellations.

Both use the same GPIOs (see PINMAP and RADIO_PINMAP; the module adapter
swaps MOSI and SCK) so firmware needs only a pin map per radio.  Routing is
done by hand in this file and checked by DRC (scripts/verify_boards.py).

GPIO choice: GPIO2/8/9 are ESP32-C3 boot strapping pins, so no socket
position that is a radio output on any board goes to them; they carry only
ESP32 outputs (RESET) or a position that is an input on every radio (the
chip select).  GPIO20/21 (UART) carry no socket position; on the socket
adapter they also reach J5, the fly-wire header beside the socket, where
GPIO20 is the SX1278's DIO2/DATA pin.
"""

from __future__ import annotations

import argparse
import pathlib
import sys

sys.path.insert(0, str(pathlib.Path(__file__).resolve().parent))
from generate_cc1101 import SMA_GND_OFFSET, SMA_PAD_L, sma_fp  # noqa: E402
from kicadgen import Design, Footprint, Model, Pad, Part, SymbolRef, Track, Via, Zone, fp_circle, fp_rect, fp_text, gr_line, gr_rect, gr_text  # noqa: E402

# ---------------------------------------------------------------------------
# Shared: GPIO assignment and SuperMini geometry
# ---------------------------------------------------------------------------
# SX1278 module adapter's assignment (see RADIO_PINMAP for the socket
# adapter's, which it matches apart from swapping MOSI and SCK).
PINMAP = {
    "DIO1": "GPIO6",  # GDO2 on the CC1101
    "MISO": "GPIO7",
    "NSS": "GPIO10",  # CSN on the CC1101; moved off the GPIO9 boot strap
    "DIO0": "GPIO20",  # GDO0 on the CC1101; moved off GPIO10 to make room for NSS
    "RESET": "GPIO21",  # SX1278 module only; moved off the GPIO8 boot strap
    "MOSI": "GPIO3",  # (GPIO4 on the socket adapter: the two swap so this adapter's bottom copper routes)
    "SCK": "GPIO4",
    "+3V3": "GPIO5",  # radio-type strap (see RADIO_ID below): tied high on this adapter
}

SM_PITCH = 2.54
SM_LEFT_X = 4.0  # left header column
SM_RIGHT_X = SM_LEFT_X + 15.24  # 19.24
SM_PIN1_Y = 4.0
SM_BODY = (SM_LEFT_X - 1.38, SM_PIN1_Y - 1.74, SM_RIGHT_X + 1.38, SM_PIN1_Y - 1.74 + 22.52)  # 2.62,2.26 .. 20.62,24.78
SM_LEFT_GPIO = ["GPIO5", "GPIO6", "GPIO7", "GPIO8", "GPIO9", "GPIO10", "GPIO20", "GPIO21"]
SM_RIGHT_GPIO = ["+5V", "GND", "+3V3", "GPIO4", "GPIO3", "GPIO2", "GPIO1", "GPIO0"]
SM_LEFT_SILK = ["5", "6", "7", "8", "9", "10", "20", "21"]  # as printed on the SuperMini
SM_RIGHT_SILK = ["5V", "G", "3V3", "4", "3", "2", "1", "0"]
SM_PAD = 1.6
SM_DRILL = 1.0
HEADER_BODY = 2.5  # plastic body of a 2.54 mm pin header: the gap between two boards it joins
SUPERMINI_MODEL = "esp32-c3-supermini.step"  # see scripts/build_3d.py for the models and their origins
TRACK = 0.25
BOARD_W = 24.0

CONN7 = SymbolRef("Connector_Generic.kicad_sym", "Connector_Generic", "Conn_01x07")
CONN8 = SymbolRef("Connector_Generic.kicad_sym", "Connector_Generic", "Conn_01x08")
CONN16 = SymbolRef("Connector_Generic.kicad_sym", "Connector_Generic", "Conn_01x16")
CONN1 = SymbolRef("Connector_Generic.kicad_sym", "Connector_Generic", "Conn_01x01")
CONN2X4 = SymbolRef("Connector_Generic.kicad_sym", "Connector_Generic", "Conn_02x04_Odd_Even")
COAX = SymbolRef("Connector.kicad_sym", "Connector", "Conn_Coaxial")
CONN2 = SymbolRef("Connector_Generic.kicad_sym", "Connector_Generic", "Conn_01x02")
RES = SymbolRef("Device.kicad_sym", "Device", "R")

# Radio-type strap: firmware reads GPIO5 (net RADIO_ID) once with the internal
# pull-down and once with the pull-up enabled, which tells the three states
# apart.  GPIO5 is not an ESP32-C3 boot strapping pin, so tying it is safe.
RADIO_ID_GPIO = "GPIO5"
RADIO_ID_STATES = {
    "floating": "CC1101 E07-M1101D in the socket adapter (no jumper on JP1, R1 not fitted)",
    "low": "SX1278 Ra-02 breakout in the socket adapter (jumper on JP1 or 0R in R1, both to GND)",
    "high": "SX1278 castellated module adapter (GPIO5 hard-wired to 3V3)",
}



def supermini_header_fp() -> Footprint:
    """1x8 row for one side of the SuperMini, pins stepping along +y, pin 1 at the origin."""
    pads = [Pad(str(i + 1), (0, i * SM_PITCH), (SM_PAD, SM_PAD), "thru_hole", "rect" if i == 0 else "circle", SM_DRILL) for i in range(8)]
    return Footprint(
        name="SuperMini_Header_1x08_P2.54mm_THT",
        descr="1x8 2.54 mm through-hole row for one side of an ESP32-C3 SuperMini (1.0 mm holes, 1.6 mm pads); pin 1 square",
        tags="ESP32-C3 SuperMini header 2.54mm",
        pads=pads,
        ref_pos=(0, -2.0, 0),
        value_pos=(0, 7 * SM_PITCH + 2.0),
    )


def sm_y(pin: int) -> float:
    return SM_PIN1_Y + (pin - 1) * SM_PITCH


def signal_net(name: str, gpio: str) -> str:
    """Net name for a SuperMini pin: the radio signal name when mapped, else the GPIO."""
    return name if name else gpio


def supermini_parts(d: Design, left_nets: dict[str, str], right_nets: dict[str, str], labels: dict[str, str] | None = None) -> None:
    """Add J1 (left row) and J2 (right row) of the SuperMini plus outline/silk.
    labels: GPIO -> silk text, overriding the net name printed inside the row."""
    labels = labels or {}
    bx, by = d.bx, d.by
    fp = supermini_header_fp()
    d.parts.append(Part("J1", fp, (bx + SM_LEFT_X, by + SM_PIN1_Y), CONN8, "Conn_01x08", left_nets, (76.2, 101.6), "ESP32-C3 SuperMini left row",
                        models=[Model(SUPERMINI_MODEL, (0, 0, HEADER_BODY))]))
    d.parts.append(Part("J2", fp, (bx + SM_RIGHT_X, by + SM_PIN1_Y), CONN8, "Conn_01x08", right_nets, (101.6, 101.6), "ESP32-C3 SuperMini right row"))
    x0, y0, x1, y1 = SM_BODY
    # Outline on F.Fab (the pin-name silk sits between the pads and the outline).
    d.graphics.append(gr_rect("sm_outline", bx + x0, by + y0, bx + x1, by + y1, "F.Fab", 0.12))
    d.graphics.append(gr_rect("sm_usb", bx + (x0 + x1) / 2 - 4.5, by + y0 - 1.5, bx + (x0 + x1) / 2 + 4.5, by + y0 + 5.85, "F.Fab", 0.1, "dash"))
    d.graphics.append(gr_text("sm_title", "ESP32-C3 SuperMini", bx + (x0 + x1) / 2, by + y1 - 1.2, "F.SilkS", 0.7))
    d.graphics.append(gr_text("sm_usb", "USB-C", bx + (x0 + x1) / 2, by + y0 + 1.0, "F.SilkS", 0.6))
    # ESP32 pin names (as printed on the SuperMini) outside each header row,
    # radio signal names inside it.
    for pin, gpio in enumerate(SM_LEFT_GPIO, 1):
        d.graphics.append(gr_text(f"esp_l{pin}", SM_LEFT_SILK[pin - 1], bx + SM_LEFT_X - 1.2, by + sm_y(pin), "F.SilkS", 0.6, "right"))
        net = left_nets[str(pin)]
        if net != gpio:
            d.graphics.append(gr_text(f"lbl_l{pin}", labels.get(gpio, net), bx + SM_LEFT_X + 1.2, by + sm_y(pin), "F.SilkS", 0.6, "left"))
    for pin, gpio in enumerate(SM_RIGHT_GPIO, 1):
        d.graphics.append(gr_text(f"esp_r{pin}", SM_RIGHT_SILK[pin - 1], bx + SM_RIGHT_X + 1.2, by + sm_y(pin), "F.SilkS", 0.6, "left"))
        net = right_nets[str(pin)]
        if net != gpio:
            d.graphics.append(gr_text(f"lbl_r{pin}", labels.get(gpio, net), bx + SM_RIGHT_X - 1.2, by + sm_y(pin), "F.SilkS", 0.6, "right"))


def supermini_nets(mapping: dict[str, str]) -> tuple[dict[str, str], dict[str, str]]:
    """mapping: signal -> GPIO.  Returns (left pad nets, right pad nets)."""
    inv = {g: s for s, g in mapping.items()}
    left = {str(i + 1): inv.get(g, g) for i, g in enumerate(SM_LEFT_GPIO)}
    right = {str(i + 1): inv.get(g, g) for i, g in enumerate(SM_RIGHT_GPIO)}
    return left, right


# ---------------------------------------------------------------------------
# Adapter A: SuperMini + SX1278 castellated module
# ---------------------------------------------------------------------------
MOD_W, MOD_H = 16.5, 17.0  # module rotated 90 deg CW: pad row on top, ANT on the bottom edge
MOD_L, MOD_T = 3.75, 31.5
MOD_R, MOD_B = MOD_L + MOD_W, MOD_T + MOD_H
ROW_PITCH = 1.27
ROW_FIRST = 1.2  # pin 1 from the module's right edge (its top corner before rotation)
LAND = (1.0, 3.0)  # row / bottom land pads: width along the edge x length across it
NOTCH_LAND = (2.0, 0.8)
VIA_Y = MOD_T - 2.1  # 29.4: via row just above the land pads
GND_TRUNK_Y = MOD_T - 1.3  # 30.2 on B.Cu
ANT_HOLE_Y = MOD_B + 3.0  # 51.5: spring antenna wire hole
SX_H = 58.0
SMA_X = 17.0  # optional edge-mount SMA jack on the bottom edge (ground legs at +/-4.25)

SX_PINS = ["GND", "DIO1", "DIO2", "DIO3", "+3V3", "MISO", "MOSI", "SCK", "NSS", "DIO0", "RESET", "GND", "DIO4", "DIO5", "GND", "ANT"]


def row_x(pin: int) -> float:
    """Absolute-from-board x of row pad for module pin 1..12."""
    return MOD_R - ROW_FIRST - (pin - 1) * ROW_PITCH


def sx1278_land_fp() -> Footprint:
    """Land pattern for the module in its rotated orientation, origin at the
    module's top-left corner on the carrier."""
    pads = []
    for pin in range(1, 13):
        pads.append(Pad(str(pin), (row_x(pin) - MOD_L, 0), LAND, "smd", "rect"))
    pads.append(Pad("13", (-0.5, 1.25), NOTCH_LAND, "smd", "rect"))
    pads.append(Pad("14", (-0.5, 2.7), NOTCH_LAND, "smd", "rect"))
    pads.append(Pad("15", (MOD_W - 2.8, MOD_H), LAND, "smd", "rect"))
    pads.append(Pad("16", (MOD_W - 1.4, MOD_H), LAND, "smd", "rect"))
    extra = [
        fp_rect("sx:outline", 0, 0, MOD_W, MOD_H, "F.Fab", 0.1),
        fp_text("sx:label", "SX1278 module", MOD_W / 2, MOD_H / 2, "F.Fab", 0.8),
        fp_text("sx:pin1", "1", MOD_W - ROW_FIRST + 1.0, -2.0, "F.SilkS", 0.6),
        fp_text("sx:pin12", "12", MOD_W - ROW_FIRST - 11 * ROW_PITCH - 1.4, -2.0, "F.SilkS", 0.6),
    ]
    return Footprint(
        name="SX1278_Module_16pin_Land",
        descr="Land pattern for the 16-pin castellated PXL1276-D01 style SX1278 module, rotated so the 12-pad row is along the top edge (pin 1 at the right) and ANT/GND on the bottom edge; pads extend 1.5 mm outside the module edge for soldering",
        tags="SX1278 LoRa module land pattern castellated",
        pads=pads,
        extra=extra,
        attr="smd",
        ref_pos=(MOD_W / 2, MOD_H / 2 + 1.5, 0),
        value_pos=(MOD_W / 2, MOD_H / 2 + 3.0),
    )


def antenna_hole_fp() -> Footprint:
    return Footprint(
        name="Antenna_Wire_Hole_1.0mm",
        descr="Through-hole for a spring / wire antenna, 1.0 mm drill, 2.0 mm pad",
        tags="antenna wire hole",
        pads=[Pad("1", (0, 0), (2.0, 2.0), "thru_hole", "circle", 1.0)],
        ref_pos=(0, -1.8, 0),
        value_pos=(0, 1.8),
    )


def build_sx1278() -> Design:
    d = Design(
        project="esp32c3-sx1278-adapter",
        title="ESP32-C3 SuperMini to SX1278 LoRa module adapter",
        comment="Carrier joining an ESP32-C3 SuperMini to a 16-pin castellated SX1278 433MHz module",
        fp_lib="Adapter",
        width=BOARD_W,
        height=SX_H,
        thickness=1.6,
        castellated_refs=["J4"],  # the SMA's edge-mount pads sit on the board edge
        sch_note="ESP32-C3 SuperMini (J1 left row, J2 right row) driving an SX1278 LoRa module (U2).\\nSPI: MOSI=GPIO3 SCK=GPIO4 NSS=GPIO10 MISO=GPIO7; RESET=GPIO21 DIO0=GPIO20 DIO1=GPIO6.  GPIO8/GPIO9 (boot straps) are left unused.\\nGPIO5 is tied to 3V3: the radio-type strap reads high on this adapter.\\nJ3 is the spring antenna wire hole; J4 an optional edge-mount SMA jack (fit one or the other).",
    )
    bx, by = d.bx, d.by
    left, right = supermini_nets(PINMAP)
    supermini_parts(d, left, right, labels={RADIO_ID_GPIO: "ID=3V3"})
    # The module model is drawn with its 12-pad edge on the left (as the reference board
    # under hardware/parts/); here it is turned 90 degrees clockwise so that edge is on top.
    d.parts.append(Part("U2", sx1278_land_fp(), (bx + MOD_L, by + MOD_T), CONN16, "SX1278_module", {str(i + 1): n for i, n in enumerate(SX_PINS)}, (127.0, 101.6), "SX1278 LoRa module",
                        models=[Model("sx1278-lora-module.step", (MOD_W, 0, 0), (0, 0, 90))]))  # KiCad applies the negated angle
    d.parts.append(Part("J3", antenna_hole_fp(), (bx + MOD_R - 1.4, by + ANT_HOLE_Y), CONN1, "Antenna", {"1": "ANT"}, (152.4, 101.6), "Spring antenna"))
    d.parts.append(Part("J4", sma_fp(), (bx + SMA_X, by + SX_H), COAX, "SMA", {"1": "ANT", "2": "GND"}, (165.1, 101.6), "Optional edge-mount SMA jack", models=[Model("sma-edge-jack.step")]))

    T = d.tracks
    V = d.vias
    F, B = "F.Cu", "B.Cu"
    pad_in = MOD_T + 0.5  # end tracks just inside the land pads (which span MOD_T -1.5 .. +1.5)

    def left_bus(pin: int, bus_x: float, lane_y: float, target_x: float, net: str) -> None:
        T.append(Track(net, F, TRACK, [(bx + SM_LEFT_X, by + sm_y(pin)), (bx + bus_x, by + sm_y(pin)), (bx + bus_x, by + lane_y), (bx + target_x, by + lane_y), (bx + target_x, by + pad_in)]))

    # F.Cu signal lanes from the left column: upper header pins take the
    # outer bus and the outer lane, and the GPIO order matches the module's
    # pad order (DIO1 17.78 > MISO 12.7 > NSS 8.89 > DIO0 7.62), so drops
    # never cross another lane.  (Pin 4, RESET, is on B.Cu.)
    left_bus(2, 7.2, 26.0, row_x(2), "DIO1")  # GPIO6 -> DIO1 pad 2
    left_bus(3, 6.7, 26.5, row_x(6), "MISO")  # GPIO7 -> MISO pad 6
    left_bus(6, 6.2, 27.0, row_x(9), "NSS")  # GPIO10 -> NSS pad 9
    left_bus(7, 5.7, 27.5, row_x(10), "DIO0")  # GPIO20 -> DIO0 pad 10
    left_bus(8, 5.2, 28.0, row_x(11), "RESET")  # GPIO21 -> RESET pad 11

    # B.Cu: power, reset and NSS (from the right column), with vias just
    # above the land pads.
    def via_to_pad(net: str, x: float) -> None:
        V.append(Via(net, (bx + x, by + VIA_Y)))
        T.append(Track(net, F, TRACK, [(bx + x, by + VIA_Y), (bx + x, by + pad_in)]))

    # Radio-type strap: GPIO5 (left pin 1) tied to 3V3 (right pin 3), across the top of the SuperMini.
    T.append(Track("+3V3", B, TRACK, [(bx + SM_LEFT_X, by + sm_y(1)), (bx + SM_RIGHT_X - 1.35, by + sm_y(1)), (bx + SM_RIGHT_X - 1.35, by + sm_y(3)), (bx + SM_RIGHT_X, by + sm_y(3))]))
    # 3V3 goes down the right of the SuperMini (inside the GND track) and
    # crosses to its pad just above the via row, clear of GND's via.
    V33_LANE_Y = VIA_Y - 0.8
    T.append(Track("+3V3", B, 0.4, [(bx + SM_RIGHT_X, by + sm_y(3)), (bx + 20.6, by + sm_y(3)), (bx + 20.6, by + V33_LANE_Y), (bx + row_x(5), by + V33_LANE_Y), (bx + row_x(5), by + VIA_Y)]))
    via_to_pad("+3V3", row_x(5))
    # SCK and MOSI from the right column (GPIO4 above GPIO3, and SCK's pad left
    # of MOSI's, so they nest).  RESET/NSS/DIO0 are on the F.Cu left bus above.
    T.append(Track("SCK", B, TRACK, [(bx + SM_RIGHT_X, by + sm_y(4)), (bx + row_x(8), by + sm_y(4)), (bx + row_x(8), by + VIA_Y)]))
    via_to_pad("SCK", row_x(8))
    T.append(Track("MOSI", B, TRACK, [(bx + SM_RIGHT_X, by + sm_y(5)), (bx + row_x(7), by + sm_y(5)), (bx + row_x(7), by + VIA_Y)]))
    via_to_pad("MOSI", row_x(7))
    # GND: down the right edge of the board, then a trunk under the land pads.
    T.append(Track("GND", B, 0.4, [(bx + SM_RIGHT_X, by + sm_y(2)), (bx + 21.5, by + sm_y(2)), (bx + 21.5, by + GND_TRUNK_Y), (bx + row_x(12), by + GND_TRUNK_Y)]))
    for x in (row_x(1), row_x(12)):
        T.append(Track("GND", B, 0.4, [(bx + x, by + GND_TRUNK_Y), (bx + x, by + VIA_Y)]))
        via_to_pad("GND", x)
    gnd_bot_x = MOD_R - 2.8
    T.append(Track("GND", B, 0.4, [(bx + gnd_bot_x, by + GND_TRUNK_Y), (bx + gnd_bot_x, by + MOD_B - 2.3)]))
    V.append(Via("GND", (bx + gnd_bot_x, by + MOD_B - 2.3)))
    T.append(Track("GND", F, TRACK, [(bx + gnd_bot_x, by + MOD_B - 2.3), (bx + gnd_bot_x, by + MOD_B + 0.5)]))
    # Antenna: module ANT pad -> wire hole -> centre pin of the optional SMA.
    T.append(Track("ANT", F, 0.5, [(bx + MOD_R - 1.4, by + MOD_B + 0.5), (bx + MOD_R - 1.4, by + ANT_HOLE_Y), (bx + SMA_X, by + SX_H - SMA_PAD_L + 0.5), (bx + SMA_X, by + SX_H - SMA_PAD_L / 2)]))
    # SMA ground legs, on B.Cu from the via feeding the module's bottom GND pad.
    leg_y = SX_H - SMA_PAD_L / 2
    # The right leg's feed skirts the antenna wire hole (at MOD_R - 1.4) on its right.
    skirt_x = MOD_R + 0.8
    T.append(Track("GND", B, 0.4, [(bx + gnd_bot_x, by + MOD_B - 2.3), (bx + gnd_bot_x, by + MOD_B + 0.8), (bx + skirt_x, by + MOD_B + 0.8), (bx + skirt_x, by + SX_H - SMA_PAD_L - 1.2), (bx + SMA_X + SMA_GND_OFFSET, by + SX_H - SMA_PAD_L - 1.2), (bx + SMA_X + SMA_GND_OFFSET, by + leg_y)]))
    T.append(Track("GND", B, 0.4, [(bx + gnd_bot_x, by + MOD_B + 0.8), (bx + SMA_X - SMA_GND_OFFSET, by + MOD_B + 0.8), (bx + SMA_X - SMA_GND_OFFSET, by + leg_y)]))
    for leg_x in (SMA_X - SMA_GND_OFFSET, SMA_X + SMA_GND_OFFSET):  # the legs' front pads via up from the B.Cu feed
        V.append(Via("GND", (bx + leg_x, by + SX_H - SMA_PAD_L - 1.2)))
        T.append(Track("GND", F, 0.4, [(bx + leg_x, by + SX_H - SMA_PAD_L - 1.2), (bx + leg_x, by + leg_y)]))

    g = d.graphics
    g.append(gr_text("ant", "ANT", bx + MOD_R - 1.4 - 1.6, by + ANT_HOLE_Y, "F.SilkS", 0.6, "right"))
    g.append(gr_text("sma", "SMA", bx + SMA_X - 1.0, by + SX_H - SMA_PAD_L - 0.8, "F.SilkS", 0.5))
    g.append(gr_text("title1", "ESP32-C3 +", bx + 6.2, by + 55.0, "F.SilkS", 0.6))
    g.append(gr_text("title2", "SX1278 433MHz", bx + 6.2, by + 56.6, "F.SilkS", 0.6))
    return d


# ---------------------------------------------------------------------------
# Adapter B: SuperMini + 2x4 socket for the E07-M1101D CC1101 board or the Ra-02 breakout
# ---------------------------------------------------------------------------

# Board geometry (mm from the board's top-left corner).
CC_W, CC_H = 29.0, 38.0  # 1.5 mm taller than the parts need: see J5
CC_OVER = 0.5  # the SuperMini body overhangs the left edge by this much, so its USB-C is clear of the board
CC_PX1 = 1.74 - CC_OVER  # x of SuperMini pin 1 in both rows (1.74 = SuperMini edge to first pin)
CC_TOP_Y = 7.0  # power row (the SuperMini's right column); its castellations face the top edge
CC_BOT_Y = CC_TOP_Y + 15.24  # GPIO row (left column)
CC_S1 = (16.48, 28.5)  # socket pin 1 (outer row, rightmost column); columns step -2.54
CC_HOLE_IN = 2.4  # mounting hole centres from the edges
CC_HOLE_D = 2.2  # M2 clearance hole
CAST_LEN, CAST_OFF = 3.4, 0.9  # keyhole pad: oval length and copper offset outboard (copper reaches 2.6 mm from the hole)
SM_EDGE = 1.38  # SuperMini pin centre to its castellated edge


def supermini_castellated_row_fp(outboard: int) -> Footprint:
    """1x8 row along +x, pin 1 at the origin, for one edge of a SuperMini that may
    either be pinned through the holes or soldered flat by its castellations.
    Each pad is a keyhole: a 1.0 mm hole at the pin with 1.6 mm wide copper
    extended outboard (outboard = -1 toward -y, +1 toward +y) to 2.6 mm from the
    hole, i.e. 1.2 mm past the SuperMini's edge, so the half-hole castellation
    lands on copper."""
    side = "Up" if outboard < 0 else "Down"
    pads = [
        Pad(str(i + 1), (i * SM_PITCH, 0), (SM_PAD, CAST_LEN), "thru_hole", "rect" if i == 0 else "oval", SM_DRILL, offset=(0, outboard * CAST_OFF))
        for i in range(8)
    ]
    return Footprint(
        name=f"SuperMini_Row_1x08_P2.54mm_THT_Castellated_{side}",
        descr=f"1x8 2.54 mm row for one edge of an ESP32-C3 SuperMini: 1.0 mm holes for header pins, 1.6 x {CAST_LEN} mm oval copper extended {side.lower()} to 2.6 mm from the hole so the SuperMini can also be soldered flat by its castellations; pin 1 square",
        tags="ESP32-C3 SuperMini castellated header 2.54mm",
        pads=pads,
        ref_pos=(-2.0, 0, 90),
        value_pos=(7 * SM_PITCH + 2.0, 0),
    )


def mounting_hole_fp() -> Footprint:
    return Footprint(
        name=f"MountingHole_{CC_HOLE_D}mm_M2",
        descr=f"M2 mounting hole, {CC_HOLE_D} mm, not plated",
        tags="mounting hole M2",
        pads=[Pad("1", (0, 0), (CC_HOLE_D, CC_HOLE_D), "np_thru_hole", "circle", CC_HOLE_D)],
        extra=[fp_circle("hole:fab", 0, 0, CC_HOLE_D / 2, "F.Fab", 0.1), fp_circle("hole:bfab", 0, 0, CC_HOLE_D / 2, "B.Fab", 0.1)],
        ref_pos=(0, -2.0, 0),
        value_pos=(0, 2.0),
    )


def e07_socket_fp() -> Footprint:
    pads = []
    for n in range(1, 9):
        col, row = (n - 1) // 2, (n - 1) % 2
        pads.append(Pad(str(n), (-col * SM_PITCH, row * SM_PITCH), (1.6, 1.6), "thru_hole", "rect" if n == 1 else "circle", 1.0))
    return Footprint(
        name="PinSocket_2x04_P2.54mm_E07",
        descr="2x4 2.54 mm socket matching the Ebyte E07-M1101D header: pin 1 square, pin 2 below it, odd pins in the outer row, columns stepping to -x",
        tags="pin socket 2.54mm 2x04 E07-M1101D",
        pads=pads,
        ref_pos=(-3 * SM_PITCH - 1.8, SM_PITCH / 2, 90),
        value_pos=(-1.5 * SM_PITCH, SM_PITCH + 2.0),
    )


def pin_header_fp(n: int, along: str = "x") -> Footprint:
    """1xN 2.54 mm through-hole pin header, pin 1 (square) at the origin and
    the pins stepping along +x (along="x") or +y (along="y")."""
    step = (SM_PITCH, 0) if along == "x" else (0, SM_PITCH)
    pads = [Pad(str(i + 1), (i * step[0], i * step[1]), (1.7, 1.7), "thru_hole", "rect" if i == 0 else "circle", 1.0) for i in range(n)]
    span = (n - 1) * SM_PITCH + 2.0
    return Footprint(
        name=f"PinHeader_1x{n:02d}_P2.54mm_Vertical" + ("" if along == "x" else "_AlongY"),
        descr=f"1x{n} 2.54 mm pin header, 1.0 mm holes, 1.7 mm pads; pin 1 square",
        tags="pin header 2.54mm",
        pads=pads,
        ref_pos=(-2.0, 0, 90) if along == "x" else (0, -2.0, 0),
        value_pos=(span, 0) if along == "x" else (0, span),
    )


def resistor_0805_fp(back: bool = False) -> Footprint:
    """0805 (2012 metric) chip resistor with hand-solder pads, pads along +y
    (pad 1 at -y), on the front or (back=True) the back copper."""
    layers = ("B.Cu", "B.Mask", "B.Paste") if back else None
    pads = [Pad("1", (0, -1.0), (1.4, 1.2), "smd", "rect", layers=layers), Pad("2", (0, 1.0), (1.4, 1.2), "smd", "rect", layers=layers)]
    return Footprint(
        name="R_0805_2012Metric_HandSolder_AlongY" + ("_Back" if back else ""),
        descr="0805 chip resistor, 1.4 x 1.2 mm pads 2.0 mm apart, pins along +y" + (", on the back copper" if back else ""),
        tags="resistor 0805 hand solder",
        pads=pads,
        extra=[fp_rect("r:body", -0.65, -1.0, 0.65, 1.0, "B.Fab" if back else "F.Fab", 0.1)],
        attr="smd",
        ref_pos=(0, -2.4, 0),
        value_pos=(0, 2.4),
    )


def header_pullup_fp() -> Footprint:
    """0805 chip resistor whose pads land on two adjacent 2.54 mm header pins (pad 1 at
    -x, pad 2 at +x), on the back copper, so it bridges a strap pin to 3V3 with no extra
    track.  Optional / do-not-populate."""
    layers = ("B.Cu", "B.Mask", "B.Paste")
    pads = [Pad("1", (-SM_PITCH / 2, 0), (1.4, 1.2), "smd", "rect", layers=layers),
            Pad("2", (SM_PITCH / 2, 0), (1.4, 1.2), "smd", "rect", layers=layers)]
    return Footprint(
        name="R_0805_HeaderPullup",
        descr="0805 resistor bridging two adjacent 2.54 mm header pins, on the back copper (optional strap pull-up)",
        tags="resistor 0805 pull-up header",
        pads=pads,
        extra=[fp_rect("r:body", -0.65, -1.0, 0.65, 1.0, "B.Fab", 0.1)],
        attr="smd",
        courtyard=False,  # it deliberately sits on the header pins
        ref_pos=(0, -1.8, 0),
        value_pos=(0, 1.8),
    )


class Carrier:
    """The parts shared by the socket-style adapters: a SuperMini on its side
    with USB-C off the left edge (keyhole pads: header pins or castellated),
    four M2 corner holes, a GND pour on F.Cu with a keepout under the
    SuperMini's ceramic antenna, and silkscreen on both sides.  All tracks go
    on B.Cu.  Coordinates handed to the helpers are mm from the board's
    top-left corner."""

    def __init__(self, project: str, title: str, comment: str, sch_note: str, mapping: dict[str, str], sig_names: dict[str, str], width: float = CC_W, height: float = CC_H):
        self.d = Design(project=project, title=title, comment=comment, fp_lib="Adapter", width=width, height=height, thickness=1.6, sch_note=sch_note)
        self.W, self.H = width, height
        self.sig_names = sig_names  # net name -> name printed on the radio board
        self.left, self.right = supermini_nets(mapping)
        self.sm_right = self.px(1) - 1.74 + 22.52  # SuperMini body right edge (22.02)
        d = self.d
        d.parts.append(Part("J1", supermini_castellated_row_fp(+1), (self.X(self.px(1)), self.Y(CC_BOT_Y)), CONN8, "Conn_01x08", self.left, (76.2, 101.6), "ESP32-C3 SuperMini GPIO row (left column)"))
        # The SuperMini model (origin at its left-column pin 1, USB-C up) rides on
        # J2: turned 90 degrees so its right column lies along the power row, on
        # top of the 2.5 mm header bodies.
        d.parts.append(Part("J2", supermini_castellated_row_fp(-1), (self.X(self.px(1)), self.Y(CC_TOP_Y)), CONN8, "Conn_01x08", self.right, (101.6, 101.6), "ESP32-C3 SuperMini power row (right column)",
                            models=[Model(SUPERMINI_MODEL, (0, -15.24, HEADER_BODY), (0, 0, -90))]))  # KiCad applies the negated angle

    # -- coordinates ----------------------------------------------------------
    def X(self, v: float) -> float:
        return self.d.bx + v

    def Y(self, v: float) -> float:
        return self.d.by + v

    @staticmethod
    def px(pin: int) -> float:
        """x of SuperMini pin 1..8 along either row."""
        return CC_PX1 + (pin - 1) * SM_PITCH

    @staticmethod
    def gap(a: float, b: float) -> float:
        return (a + b) / 2

    # -- parts ------------------------------------------------------------------
    def add(self, ref: str, fp: Footprint, at: tuple[float, float], sym: SymbolRef, value: str, nets: dict[str, str], sch_at: tuple[float, float], descr: str, models: list[Model] | None = None) -> None:
        self.d.parts.append(Part(ref, fp, (self.X(at[0]), self.Y(at[1])), sym, value, nets, sch_at, descr, models or []))

    def holes(self, h1_models: list[Model] | None = None) -> None:
        """Four M2 corner holes; H1 (top left) can carry models drawn in the
        board's frame with their origin at that hole, e.g. the printed case."""
        fp = mounting_hole_fp()
        sym = SymbolRef("Mechanical.kicad_sym", "Mechanical", "MountingHole")
        corners = [(CC_HOLE_IN, CC_HOLE_IN), (self.W - CC_HOLE_IN, CC_HOLE_IN), (CC_HOLE_IN, self.H - CC_HOLE_IN), (self.W - CC_HOLE_IN, self.H - CC_HOLE_IN)]
        for i, (hx, hy) in enumerate(corners, 1):
            self.add(f"H{i}", fp, (hx, hy), sym, "MountingHole", {}, (152.4 + (i - 1) * 12.7, 101.6), "M2 mounting hole", models=h1_models if i == 1 else None)

    def track(self, net: str, width: float, pts: list[tuple[float, float]], layer: str = "B.Cu") -> None:
        self.d.tracks.append(Track(net, layer, width, [(self.X(x), self.Y(y)) for x, y in pts]))

    def zones(self) -> None:
        """GND pour on the front, kept away from the SuperMini's ceramic antenna
        (the 3.8 mm of the module furthest from the USB-C); the keepout also
        bars tracks on both layers there."""
        X, Y, TOP, BOT = self.X, self.Y, CC_TOP_Y, CC_BOT_Y
        x0, x1, y0, y1 = self.sm_right - 3.8, self.sm_right + 0.1, TOP + 1.6, BOT - 1.3
        self.d.zones.append(Zone("", ("F.Cu", "B.Cu"), "antenna_keepout", [(X(x0), Y(y0)), (X(x1), Y(y0)), (X(x1), Y(y1)), (X(x0), Y(y1))], keepout_tracks=True))
        m = 0.3
        self.d.zones.append(Zone("GND", ("F.Cu",), "gnd_pour", [(X(m), Y(m)), (X(self.W - m), Y(m)), (X(self.W - m), Y(self.H - m)), (X(m), Y(self.H - m))]))

    # -- silkscreen, front and back --------------------------------------------
    MIRROR = {None: "mirror", "left": "right mirror", "right": "left mirror"}

    def silk(self, key: str, text: str, x: float, y: float, size: float, justify: str | None = None, angle: float = 0) -> None:
        """Text on both silk layers; the back copy is mirrored about its anchor
        so it reads correctly from the back and keeps its side of the anchor."""
        g = self.d.graphics
        g.append(gr_text(f"{key}:f", text, self.X(x), self.Y(y), "F.SilkS", size, justify, angle))
        g.append(gr_text(f"{key}:b", text, self.X(x), self.Y(y), "B.SilkS", size, self.MIRROR[justify], (-angle) % 360))

    def both(self, fn, key: str, coords: tuple[float, ...], width: float, layers: tuple[str, str] = ("F.SilkS", "B.SilkS"), stype: str = "solid", bstype: str | None = None) -> None:
        """A gr_line / gr_rect on a pair of layers (front and back).  On the
        silk the back copy is dashed unless told otherwise: the back carries
        the tracks, and a dashed outline reads as "the part is on the other
        side" there."""
        if bstype is None:
            bstype = "dash" if layers[1] == "B.SilkS" else stype
        for suffix, layer, st in zip("fb", layers, (stype, bstype)):
            self.d.graphics.append(fn(f"{key}:{suffix}", *(self.X(v) if i % 2 == 0 else self.Y(v) for i, v in enumerate(coords)), layer, width, st))

    def row_pad_boxes(self, row_y: float, outboard: int) -> list[tuple[float, float, float, float]]:
        """Bounding boxes of one SuperMini keyhole row's pads (see supermini_castellated_row_fp)."""
        cy = row_y + outboard * CAST_OFF
        return [(self.px(i) - SM_PAD / 2, cy - CAST_LEN / 2, self.px(i) + SM_PAD / 2, cy + CAST_LEN / 2) for i in range(1, 9)]

    def silk_gapped(self, key: str, p0: tuple[float, float], p1: tuple[float, float], blocks: list[tuple[float, float, float, float]],
                    clear: float = 0.2, width: float = 0.12, min_len: float = 0.4) -> None:
        """An axis-aligned line on both silk layers, broken wherever it would
        cross one of `blocks` (x0 y0 x1 y1, grown by `clear`); pieces shorter
        than min_len are dropped rather than printed as specks."""
        (ax, ay), (bx, by) = p0, p1
        horiz = ay == by
        lo, hi = sorted((ax, bx) if horiz else (ay, by))
        here = ay if horiz else ax
        cuts = sorted((c0 - clear, c1 + clear) for x0, y0, x1, y1 in blocks
                      for (a, b), (c0, c1) in [(((y0, y1), (x0, x1)) if horiz else ((x0, x1), (y0, y1)))]
                      if a - clear <= here <= b + clear)
        at, segs = lo, []
        for c0, c1 in cuts:
            if c0 > at:
                segs.append((at, min(c0, hi)))
            at = max(at, c1)
        if at < hi:
            segs.append((at, hi))
        for i, (s0, s1) in enumerate(segs):
            if s1 - s0 >= min_len:
                self.both(gr_line, f"{key}{i}", (s0, ay, s1, by) if horiz else (ax, s0, bx, s1), width)

    def supermini_silk(self) -> None:
        px, TOP, BOT = self.px, CC_TOP_Y, CC_BOT_Y
        # Body: full outline on the fab layers, and on silk too -- it is the
        # SuperMini's mechanical envelope, so nothing else may go inside it.
        # The long edges run through the keyhole pads, so they are printed as
        # the pieces that fit in the gaps between pins.
        x0, y0, x1, y1 = px(1) - 1.74, TOP - SM_EDGE, self.sm_right, BOT + SM_EDGE
        self.both(gr_line, "sm_top", (0.0, y0, x1, y0), 0.1, layers=("F.Fab", "B.Fab"))
        self.both(gr_line, "sm_bot", (0.0, y1, x1, y1), 0.1, layers=("F.Fab", "B.Fab"))
        self.both(gr_line, "sm_right", (x1, y0, x1, y1), 0.1, layers=("F.Fab", "B.Fab"))
        usb = (0.2, (y0 + y1) / 2 - 4.5, x0 + 5.85, (y0 + y1) / 2 + 4.5)  # the USB-C receptacle's plan view: 9 mm wide, 5.85 mm onto the board
        self.both(gr_rect, "sm_usb", usb, 0.1, layers=("F.Fab", "B.Fab"), stype="dash")
        self.both(gr_rect, "sm_usb_silk", usb, 0.12)  # the USB-C's plan-view outline, on the silk too
        self.both(gr_line, "sm_silk_right", (x1, y0, x1, y1), 0.12)
        rows = self.row_pad_boxes(TOP, -1) + self.row_pad_boxes(BOT, +1)
        self.silk_gapped("sm_silk_top", (0.0, y0), (x1, y0), rows)
        self.silk_gapped("sm_silk_bot", (0.0, y1), (x1, y1), rows)
        self.silk("sm_title", "ESP32-C3 SuperMini", (x0 + x1 + 5.85) / 2, (y0 + y1) / 2, 0.7)  # centred in the room right of the USB-C
        # ESP32 pin names (as printed on the SuperMini) outside each row, beyond
        # the keyhole copper; inside the rows, what each pin does on this board:
        # the radio signal it carries, or where else it goes (sig_names).
        for pin in range(1, 9):
            self.silk(f"esp_t{pin}", SM_RIGHT_SILK[pin - 1], px(pin), TOP - 3.1, 0.5)
            self.silk(f"esp_b{pin}", SM_LEFT_SILK[pin - 1], px(pin), BOT + 3.1, 0.5)
            for row, nets, gpios, y, sign in (("t", self.right, SM_RIGHT_GPIO, TOP, +1), ("b", self.left, SM_LEFT_GPIO, BOT, -1)):
                net = nets[str(pin)]
                lab = self.sig_names.get(net, None if net == gpios[pin - 1] else net)
                if not lab:
                    continue
                if px(pin) < usb[2]:
                    # Under the USB-C outline only the 2.3 mm between the pad's
                    # ring and the outline is free: centre the label there, and
                    # print a two-part name as two lines.
                    room = usb[1] - (TOP + SM_PAD / 2) - 0.3
                    yc = y + sign * (SM_PAD / 2 + 0.15 + room / 2)
                    lines = lab.split("/") if 0.95 * 0.5 * len(lab) > room else [lab]
                    for i, part in enumerate(lines):
                        self.silk(f"sig_{row}{pin}_{i}", part, px(pin) + (i - (len(lines) - 1) / 2) * 0.8, yc, 0.5, None, 90)
                else:
                    self.silk(f"sig_{row}{pin}", lab, px(pin), y + sign * (2.7 + 0.2 * max(0, len(lab) - 4)), 0.5, None, 90)

    def title_silk(self, title: str) -> None:
        """Board title in the strip right of the SuperMini, and a note on the
        front that the parts go on that side."""
        self.silk("title", title, self.W - 2.8, self.H / 2, 0.7, None, 90)
        self.d.graphics.append(gr_text("side:f", "parts this side", self.X(self.W - 1.3), self.Y(self.H / 2), "F.SilkS", 0.5, None, 90))


# Socket-adapter geometry (mm).  Everything below is routed on B.Cu alone.
SOCKET_Y = 30.5  # socket outer row; inner row 2.54 below
LANES = [CC_BOT_Y + 3.05 + i * 0.5 for i in range(4)]  # 25.29 .. 26.79: lanes under the GPIO row's keyhole copper (to 24.84)
LANE_A = LANES[0]  # GPIO21's lane, above J5's pads; GPIO20 takes J5_LANE, below them
UNDER_Y = 34.95  # GND lane under the socket (pads reach 33.84), clear of the bottom holes
GDO2_X, GDO2_Y = 5.9, 34.4  # GDO2/DIO0 goes down the left of the socket and enters its pad from below
TOP_GND_Y, TOP_3V3_Y = 0.75, 1.2  # GND and 3V3 lanes along the top edge, above the expansion header
GND_RISE_X, V33_RISE_X = 4.3, 5.6  # where they leave the power row, between the top-left hole and header pin 1
STRIP = {"GPIO21": 22.9, "GPIO20": 23.35, "+3V3": 24.55, "GND": 25.0}  # lanes down the strip right of the SuperMini
MID_A, MID_B = CC_BOT_Y - 1.74, CC_BOT_Y - 1.24  # 20.5 / 21.0: jogs between the rows, just above the GPIO row's rings (21.44)
GPIO8_RISE_X = 9.5  # GPIO8 climbs between the GPIO3 and GPIO4 drops to reach the header
# GPIO9's pull-up R4 sits on the back between the rows, above GPIO9's pad.
# GPIO9 is boxed in on the back copper: SCK's drop passes left of its pad
# and CSN's right of it, and SCK has to enter socket pin 5 from directly
# below it.  So SCK's drop moves one gap left (to 10.13) as soon as it
# leaves its pad, and 3V3 comes down from J4 pin 3 through the power row's
# gap between GPIO3 and GPIO2 into R4's top pad; R4's bottom pad drops
# straight into GPIO9.  CSN's drop keeps right of R4 until it is above the
# GPIO row's rings, then steps into the gap between GPIO9 and GPIO10.
SCK_JOG_Y = 9.5  # SCK leaves its pad downward and steps left here, above R4
V33_DROP_X = 12.67  # 3V3 for R4: down the power row's gap between GPIO3 (11.4) and GPIO2 (13.94)
R4_X, R4_Y = 11.4, 12.5  # pads at 11.5 (+3V3) and 13.5 (GPIO9), in GPIO9's column
CSN_X = 13.3  # CSN's drop right of R4; it steps to 12.67 at MID_B to pass the GPIO row


# Socket net -> GPIO.  The socket also takes the green D-Sun CC1101 board,
# whose signals sit in a different order, with a different pin map in
# firmware; so NO socket position may be a boot strapping pin (GPIO2/8/9).
# A radio pin on a strap loads it enough that, through the ESP32's weak
# internal pull-up, it rises too slowly for the ROM to read it high at reset:
# the chip straps into USB download mode and never runs the app (measured on
# the bench, 2026-09-06).  Position 4 (CSN_NSS) therefore takes GPIO1; GPIO9
# is left unconnected -- an unconnected strap floats high on the internal
# pull-up, the safest state -- and GPIO8/GPIO2 stay on the header with pull-ups.
RADIO_PINMAP = {"MOSI": "GPIO4", "SCK": "GPIO3", "CSN_NSS": "GPIO1", "GDO0_RST": "GPIO10", "MISO": "GPIO7", "GDO2_DIO0": "GPIO6", "RADIO_ID": RADIO_ID_GPIO}
# Expansion header J4 on the top edge, centred between the mounting holes:
# 3V3 plus every GPIO the radio does not use (5V cannot be reached on one
# layer: the top-left hole sits over its pad).  GPIO2/0 rise straight from
# the power row, GPIO8 climbs from the GPIO row between the rows, and
# GPIO21/20 come from the GPIO row up the right-hand strip.  Each boot
# strap on the header (GPIO8, GPIO2) has a 3V3 pin on its left for its
# pull-up (R2, R3); the second 3V3, pin 3, also feeds R4, the GPIO9 pull-up.
EXP_PINS = ["+3V3", "GPIO8", "+3V3", "GPIO2", "GPIO0", "GPIO21", "GPIO20"]
EXP_UART = {"GPIO21": "TX", "GPIO20": "RX"}  # UART0 on the ESP32-C3
EXP_LABELS = {"+3V3": "3V3", "GPIO8": "8", "GPIO2": "2", "GPIO0": "0", "GPIO21": "21", "GPIO20": "20"}
EXP_Y = 2.55  # header row: pads clear the top lanes above and the jog row below
EXP_X1 = CC_W / 2 - 3 * SM_PITCH  # 6.88: pin 1 of the 7-pin header, so pin 4 is on the board's centre line
EXP_JOG_Y = CC_TOP_Y - 3.0  # 4.0: jogs between the power-row keyhole copper (to 4.4) and the header
# Radio-type strap in the bottom-left corner, left of the plugged-in radio
# board: JP1 (1x2 header, pin 1 = RADIO_ID, pin 2 = GND) with R1 (0805 on
# the back, in parallel) beside it.  RADIO_ID is GPIO5, the first GPIO-row
# pin, which drops straight down to it; GND arrives along the under-socket lane.
JP1_X, JP1_Y = 2.0, 30.4
R1_X, R1_Y = 4.2, JP1_Y + 1.0  # pads at JP1_Y (RADIO_ID) and JP1_Y + 2.0 (GND)
# Fly-wire header J5, in the 5.58 mm band between the SuperMini's body
# (to y = 23.62) and the top edge of the plugged-in radio board (y = 29.2):
# the only place on this board clear of both in plan view, since a 2.54 mm
# header body and both boards all sit at board level.  It carries the two
# GPIOs the radio does not use, GPIO21 and GPIO20 (which stay on J4 as well
# -- one net, brought out twice).  GPIO20 is the SX1278's DIO2/DATA pin: in
# the SX1278's continuous mode the raw bitstream leaves the chip only on
# DIO2, so an Ra-02 breakout needs one wire from its DIO2 pad to this header
# before the firmware can decode or key OOK.  GPIO21's lane passes above the
# pads and GPIO20's strip lane runs up through pin 2, so neither crosses the
# other; GND cannot be brought here on one layer (it would have to cross the
# 3V3 strip lane), and is not needed -- the boards share GND through J3.
J5_X, J5_Y = 20.81, 26.5  # pin 1; pin 2 lands on GPIO20's strip lane at 23.35
J5_LANE = 27.8  # GPIO20's lane, below J5's pads and clear of the socket's rings
# Socket pin -> net, numbered like the E07-M1101D header (pin 1 at the right
# of the outer row, columns to -x, even pins in the inner row).  The Ra-02
# breakout's header has the same layout apart from two positions, so it plugs
# into the same socket: its RST lands on GDO0's pin and its DIO0 on GDO2's.
RADIO_PINS = {"1": "GND", "2": "+3V3", "3": "GDO0_RST", "4": "CSN_NSS", "5": "SCK", "6": "MOSI", "7": "MISO", "8": "GDO2_DIO0"}
E07_LABELS = {"1": "GND", "2": "VCC", "3": "GDO0", "4": "CSN", "5": "SCK", "6": "MOSI", "7": "MISO", "8": "GDO2"}
RA02_AT_SOCKET = {"1": "GND", "2": "3V3", "3": "RST", "4": "NSS", "5": "SCK", "6": "MOSI", "7": "MISO", "8": "DIO0"}
# Net -> silk inside the SuperMini's rows: the radio signal on that pin, or
# where a spare pin goes instead (J4 / J5, R4), so every pin reads as something.
RADIO_NAMES = {"CSN_NSS": "CSN/NSS", "GDO0_RST": "GDO0/RST", "GDO2_DIO0": "GDO2/DIO0",
               "+5V": "NC", "GND": "GND", "+3V3": "3V3", "GPIO2": "J4", "GPIO0": "J4", "GPIO8": "J4",
               "GPIO9": "R4", "GPIO21": "J4/J5", "GPIO20": "DIO2", "RADIO_ID": "JP1"}
RA02_W, RA02_H, RA02_ROW_IN = 17.5, 22.5, 1.3  # Ra-02 breakout outline for the fab drawing (see generate_ra02_breakout.py)
E07_W, E07_H, E07_ROW_IN = 15.0, 30.0, 1.6


# 3D: the plugged-in radio board rides on J3 (origin = socket pin 1), on
# top of its own header's body; the E07's model origin is its pin 1, the
# Ra-02 breakout's is its pin 1 which sits three columns to the left.
RADIO_MODELS = {  # build_radio(radio=...) -> the models on J3
    "e07": [Model("cc1101-e07-m1101d.step", (0, 0, HEADER_BODY))],
    "ra02": [Model("sx1278-ra02-breakout.step", (-3 * SM_PITCH, 0, HEADER_BODY)), Model("sx1278-ra02-pigtail.step", (-3 * SM_PITCH, 0, HEADER_BODY))],
    "none": [],
}
CASE_LIFT = 12.0  # the exploded view lifts the top half this far: its skirt (at z 3.3) clears the headers (8.5) with room to see in
# A half on its own: KiCad always draws the adapter, so the half is moved to
# put its 2 mm floor (bottom half, z -5.1 to -3.1) or ceiling (top half, z 9.6
# to 11.6) round the 1.6 mm board (z -1.6 to 0), which hides it.
CASE_SINK_BOTTOM, CASE_SINK_TOP = 3.3, -11.4
CASE_BOTTOM, CASE_TOP, CASE_TOP_SLOT = "esp32c3-radio-adapter-case-bottom.step", "esp32c3-radio-adapter-case-top.step", "esp32c3-radio-adapter-case-top-slot.step"
CASE_MODELS = {  # build_radio(case=...) -> the printed case's halves on H1 (scripts/build_case.py)
    None: [],
    "open": [Model(CASE_BOTTOM)],
    "closed": [Model(CASE_BOTTOM), Model(CASE_TOP)],
    "closed-slot": [Model(CASE_BOTTOM), Model(CASE_TOP_SLOT)],  # the top half with the slot over J4
    "exploded": [Model(CASE_BOTTOM), Model(CASE_TOP, (0, 0, CASE_LIFT))],
    "bottom": [Model(CASE_BOTTOM, (0, 0, CASE_SINK_BOTTOM))],
    "top": [Model(CASE_TOP, (0, 0, CASE_SINK_TOP))],
}
CASE_ALONE = ("bottom", "top")  # the case options that show a half by itself, without any board or part


def build_radio(radio: str = "e07", case: str | None = None) -> Design:
    """SuperMini + one 2x4 socket that takes either the E07-M1101D (CC1101)
    board or the SX1278 Ra-02 breakout.  The SuperMini's right column becomes
    the top row (5V at the left) and its left column the bottom row (GPIO5 at
    the left), 15.24 mm apart; the socket sits below, shifted right so either
    plugged-in board clears the bottom-left mounting screw.

    Everything is routed on B.Cu.  The GPIO assignment keeps every socket
    position that is a radio output on any of the three boards off the boot
    strapping pins (see RADIO_PINMAP) and still routes on one layer: from
    the GPIO row, which faces the socket, GDO0 (GPIO10) drops straight in,
    MISO (GPIO7) takes a short lane into the column under GPIO8's pad and
    GDO2 (GPIO6) goes round the left of the socket into its pad from below;
    SCK and MOSI (GPIO3, GPIO4) and CSN (GPIO1) come from the power row,
    down between the rows: SCK and MOSI through the gaps either side of
    GPIO8's pad, while GPIO8 climbs between them to the header, and CSN
    through the gap right of GPIO9.  GND and 3V3 leave the power row
    upward, run along the top edge above the expansion header and down the
    strip right of the SuperMini into the socket's right column.  GPIO2/0
    rise straight into the header; GPIO21/20 reach it up the same strip,
    GPIO21 by way of the lane above J5 and GPIO20 through J5's pin 2 pad.
    GPIO5 drops to the strap.  GPIO9's pull-up R4 sits between the rows in
    its column, fed with 3V3 from J4 pin 3 down through the power row.

    `radio` picks the board in the socket for the 3D view ("e07", "ra02" or
    "none"); `case` adds the printed case's halves on H1: "open" (the bottom
    half only), "closed" (both halves snapped together), "exploded" (the top
    half lifted CASE_LIFT clear), or "bottom" / "top" for that half by itself
    with no board or part models at all (the adapter, which KiCad always
    draws, is hidden inside the half's floor or ceiling).  The committed
    board has no case."""
    if radio not in RADIO_MODELS:
        raise ValueError(f"radio must be one of {sorted(RADIO_MODELS)}, not {radio!r}")
    if case not in CASE_MODELS:
        raise ValueError(f"case must be one of {sorted(k for k in CASE_MODELS if k)} or None, not {case!r}")
    c = Carrier(
        project="esp32c3-radio-adapter",
        title="ESP32-C3 SuperMini to CC1101 (E07-M1101D, D-Sun) or SX1278 Ra-02 breakout adapter",
        comment="Carrier joining an ESP32-C3 SuperMini to a CC1101 board (Ebyte E07-M1101D-SMA or D-Sun) or an SX1278 Ra-02 breakout via one 2x4 socket; all tracks on the back, GND pour on the front",
        sch_note="ESP32-C3 SuperMini (J1 = GPIO row, J2 = power row; through-hole or castellated) driving a CC1101 E07-M1101D board or an SX1278 Ra-02 breakout in socket J3.\\nSocket positions 3..8 = GPIO10, 1, 3, 4, 7, 6 (blue E07: GDO0 CSN SCK MOSI MISO GDO2; green D-Sun: MOSI SCK MISO GDO2 GDO0 CSN; Ra-02: RST NSS SCK MOSI MISO DIO0).  GPIO9 (a boot strap) carries no radio pin: CSN/SCK/NSS moved to GPIO1 so no radio pin loads a strap; R4 is an optional pull-up on it.\\nJ4: a 2nd 3V3, the unused GPIOs, and optional pull-ups (R2/R3) on the GPIO8/GPIO2 straps.  JP1 (jumper) or R1 (0R): radio-type strap on GPIO5 (RADIO_ID) to GND, open = CC1101, fitted = Ra-02.\\nJ5: fly-wire header between the SuperMini and the radio board, GPIO21 and GPIO20 (both also on J4); GPIO20 is DIO2/DATA on an SX1278.\\nH1-H4: M2 mounting holes.  All tracks on B.Cu; F.Cu carries only a GND pour.",
        mapping=RADIO_PINMAP,
        sig_names=RADIO_NAMES,
    )
    px, gap, TOP, BOT = c.px, c.gap, CC_TOP_Y, CC_BOT_Y
    ex = lambda k: EXP_X1 + (k - 1) * SM_PITCH  # noqa: E731  expansion header pin k (1..7)
    S1 = (16.48, SOCKET_Y)  # pin 1 (outer row, rightmost column); columns step -2.54
    sx = lambda pin: S1[0] - ((pin - 1) // 2) * SM_PITCH  # noqa: E731
    sy = lambda pin: S1[1] + ((pin - 1) % 2) * SM_PITCH  # noqa: E731
    SY0, SY1 = sy(1), sy(2)
    c.add("J3", e07_socket_fp(), S1, CONN2X4, "E07-M1101D_or_Ra-02", RADIO_PINS, (127.0, 101.6), "Radio board socket (CC1101 E07-M1101D or SX1278 Ra-02 breakout)", models=RADIO_MODELS[radio])
    c.add("J4", pin_header_fp(len(EXP_PINS)), (ex(1), EXP_Y), CONN7, "Expansion", {str(i + 1): n for i, n in enumerate(EXP_PINS)}, (152.4, 127.0), "3V3 and the unused GPIOs", models=[Model("pin-header-1x07.step")])
    jp1_models = [Model("pin-header-1x02.step")] + ([Model("jumper-cap.step")] if radio == "ra02" else [])
    c.add("JP1", pin_header_fp(2, "y"), (JP1_X, JP1_Y), CONN2, "RA-02", {"1": "RADIO_ID", "2": "GND"}, (177.8, 127.0), "Radio-type strap: fit a jumper for the Ra-02 breakout, leave open for the CC1101", models=jp1_models)
    c.add("R1", resistor_0805_fp(back=True), (R1_X, R1_Y), RES, "0R", {"1": "RADIO_ID", "2": "GND"}, (203.2, 127.0), "Radio-type strap, alternative to JP1: fit 0R for the Ra-02 breakout", models=[Model("r0805.step", (0, 0, -1.6), (180, 0, 0))])
    # Optional strap pull-ups: 0805s bridging a spare boot-strap header pin to the
    # 3V3 pin on its left, biasing it high at reset if that pin is ever wired to a
    # load that could hold it low at power-up.  Do-not-populate by default (the pins
    # float high on the internal pull-ups).  GPIO9 -- the strap the socket used to
    # carry -- is not on the header, so its pull-up R4 is an ordinary 0805 on the
    # back, between the rows above its pad (see R4_X).
    hp = header_pullup_fp()
    c.add("R2", hp, ((ex(1) + ex(2)) / 2, EXP_Y), RES, "4k7", {"1": "+3V3", "2": "GPIO8"}, (228.6, 127.0), "Optional pull-up: GPIO8 boot strap to 3V3 (DNP unless needed)")
    c.add("R3", hp, ((ex(3) + ex(4)) / 2, EXP_Y), RES, "4k7", {"1": "+3V3", "2": "GPIO2"}, (241.3, 127.0), "Optional pull-up: GPIO2 boot strap to 3V3 (DNP unless needed)")
    c.add("R4", resistor_0805_fp(back=True), (R4_X, R4_Y), RES, "4k7", {"1": "+3V3", "2": "GPIO9"}, (254.0, 127.0), "Optional pull-up: GPIO9 boot strap to 3V3 (DNP unless needed)")
    c.add("J5", pin_header_fp(2), (J5_X, J5_Y), CONN2, "DIO2/DATA", {"1": "GPIO21", "2": "GPIO20"}, (152.4, 152.4),
          "Fly-wire header beside the socket: pin 2 (GPIO20) is the SX1278's DIO2/DATA raw-bitstream pin, pin 1 (GPIO21) a spare",
          models=[Model("pin-header-1x02.step", (0, 0, 0), (0, 0, -90))])  # the model's pins step along +y, so turn it to lie along +x
    # The printed case (scripts/build_case.py) hangs off H1 in the renders.
    c.holes(CASE_MODELS[case])
    if case in CASE_ALONE:
        for part in c.d.parts:
            if part.ref != "H1":
                part.models = []

    g = lambda a, b: gap(px(a), px(b))  # noqa: E731  gap between two SuperMini pins
    L1, L2, L3, L4 = LANES
    # Radio signals from the GPIO row into the socket.
    c.track("GDO0_RST", TRACK, [(px(6), BOT), (sx(3), SY0)])  # GPIO10 straight down (13.94)
    # CSN/NSS (GPIO1, power row) drops between the rows, crosses to just right
    # of R4, steps into the GPIO9/GPIO10 gap above the GPIO row's rings and
    # enters socket pad 4 from the left.  GPIO9 (the strap it replaces) carries
    # only R4.
    c.track("CSN_NSS", TRACK, [(px(7), TOP), (px(7), TOP + 5.0), (CSN_X, TOP + 5.0), (CSN_X, MID_B), (gap(sx(5), sx(3)), MID_B), (gap(sx(5), sx(3)), SY1), (sx(4), SY1)])
    # MISO (GPIO7) into pin 7 from above, through the column GPIO8's pad
    # leaves free below it; GDO2/DIO0 (GPIO6) round the left of the socket
    # into pin 8 from below.
    c.track("MISO", TRACK, [(px(3), BOT), (px(3), L3), (sx(7), L3), (sx(7), SY0)])
    c.track("GDO2_DIO0", TRACK, [(px(2), BOT), (px(2), L4), (GDO2_X, L4), (GDO2_X, GDO2_Y), (sx(8), GDO2_Y), (sx(8), SY1)])
    # SCK (GPIO3) and MOSI (GPIO4) come from the power row: down between the
    # rows, through the gaps either side of GPIO8's pad, and into socket
    # pins 5 (from above) and 6 (from the left).
    c.track("SCK", TRACK, [(px(5), TOP), (px(5), SCK_JOG_Y), (g(4, 5), SCK_JOG_Y), (g(4, 5), L1), (sx(5), L1), (sx(5), SY0)])
    c.track("MOSI", TRACK, [(px(4), TOP), (px(4), MID_A), (g(3, 4), MID_A), (g(3, 4), L2), (gap(sx(7), sx(5)), L2), (gap(sx(7), sx(5)), SY1), (sx(6), SY1)])
    # GPIO8 (spare) climbs between those two drops, through the power row's
    # gap between GPIO4 and GPIO3, to the header.
    c.track("GPIO8", TRACK, [(px(4), BOT), (px(4), BOT - 0.64), (GPIO8_RISE_X, BOT - 0.64), (GPIO8_RISE_X, TOP + 1.3), (g(4, 5), TOP + 1.3), (g(4, 5), EXP_JOG_Y), (ex(2), EXP_JOG_Y), (ex(2), EXP_Y)])
    # GND and 3V3: up from the power row, along the top edge, down the strip.
    c.track("GND", TRACK, [(px(2), TOP), (GND_RISE_X, TOP - 1.5), (GND_RISE_X, TOP_GND_Y), (STRIP["GND"], TOP_GND_Y), (STRIP["GND"], UNDER_Y), (R1_X, UNDER_Y), (R1_X, R1_Y + 1.0)])
    c.track("GND", TRACK, [(gap(sx(3), sx(1)), UNDER_Y), (gap(sx(3), sx(1)), SY0), (sx(1), SY0)])  # branch up into socket pin 1
    c.track("GND", TRACK, [(R1_X, JP1_Y + 2.3), (JP1_X, JP1_Y + 2.3)])  # R1 pad 2 to JP1 pin 2
    c.track("+3V3", TRACK, [(px(3), TOP), (V33_RISE_X, TOP - 1.5), (V33_RISE_X, TOP_3V3_Y), (STRIP["+3V3"], TOP_3V3_Y), (STRIP["+3V3"], SY1), (sx(2), SY1)])
    c.track("+3V3", TRACK, [(V33_RISE_X, EXP_Y), (ex(1), EXP_Y)])  # header pin 1
    c.track("+3V3", TRACK, [(ex(3), TOP_3V3_Y), (ex(3), EXP_Y)])  # header pin 3: a second 3V3, tapped off the top 3V3 lane
    # ... and on from that pin down through the power row into R4, GPIO9's
    # pull-up, whose other pad drops into GPIO9.
    c.track("+3V3", TRACK, [(ex(3), EXP_Y), (V33_DROP_X, EXP_Y + 1.05), (V33_DROP_X, R4_Y - 1.0), (R4_X, R4_Y - 1.0)])
    c.track("GPIO9", TRACK, [(R4_X, R4_Y + 1.0), (px(5), BOT)])
    # Expansion header: GPIO2 and GPIO0 straight up with a jog to the centred
    # pins; GPIO21 and GPIO20 down the GPIO row's right end and up the strip.
    for k, pin in ((4, 6), (5, 8)):  # GPIO2 -> ex4, GPIO0 -> ex5
        c.track(SM_RIGHT_GPIO[pin - 1], TRACK, [(px(pin), TOP), (px(pin), EXP_JOG_Y), (ex(k), EXP_JOG_Y), (ex(k), EXP_Y)])
    # GPIO21 takes the lane above J5 (it drops right of GPIO20, so it must be
    # the upper of the two) and stubs down into J5 pin 1; GPIO20 takes the lane
    # below J5 and climbs the strip straight through its own pad, J5 pin 2.
    c.track("GPIO21", TRACK, [(px(8), BOT), (px(8), LANE_A), (STRIP["GPIO21"], LANE_A), (STRIP["GPIO21"], EXP_JOG_Y), (ex(6), EXP_JOG_Y), (ex(6), EXP_Y)])
    c.track("GPIO21", TRACK, [(J5_X, LANE_A), (J5_X, J5_Y)])
    c.track("GPIO20", TRACK, [(px(7), BOT), (px(7), BOT - 1.24), (g(7, 8), BOT - 1.24), (g(7, 8), J5_LANE), (STRIP["GPIO20"], J5_LANE), (STRIP["GPIO20"], EXP_Y), (ex(7), EXP_Y)])
    # Strap: GPIO5 straight down to JP1 pin 1 and across to R1 pad 1.
    c.track("RADIO_ID", TRACK, [(px(1), BOT), (px(1), JP1_Y - 1.5), (JP1_X, JP1_Y), (R1_X, JP1_Y)])
    c.zones()

    c.supermini_silk()
    c.both(gr_rect, "sockbox", (sx(7) - 1.3, SY0 - 1.3, sx(1) + 1.3, SY1 + 1.3), 0.12)
    c.silk("sock1", "1", sx(1) + 1.9, SY0, 0.6, "left")
    c.silk("sock2", "2", sx(1) + 1.9, SY1, 0.6, "left")
    # Socket labels: the E07-M1101D's names next to the socket and, where the
    # Ra-02 breakout's differ, its names in parentheses one line further out.
    for n, lab in E07_LABELS.items():
        pin = int(n)
        near, far = (SY0 - 2.0, SY0 - 2.85) if pin % 2 else (SY1 + 2.0, SY1 + 2.85)
        c.silk(f"socklbl{n}", lab, sx(pin), near, 0.5)
        if RA02_AT_SOCKET[n] != lab:
            c.silk(f"socklbl_ra{n}", f"({RA02_AT_SOCKET[n]})", sx(pin), far, 0.5)
    # Outlines of the two boards as plugged in (header edge above the outer
    # row; both extend past the bottom edge), on the fab layers.
    mx = gap(sx(7), sx(1))
    c.both(gr_rect, "e07_outline", (mx - E07_W / 2, SY0 - E07_ROW_IN, mx + E07_W / 2, CC_H - 0.3), 0.1, layers=("F.Fab", "B.Fab"), stype="dash")
    c.both(gr_rect, "ra02_outline", (mx - RA02_W / 2, SY0 - RA02_ROW_IN, mx + RA02_W / 2, CC_H - 0.5), 0.1, layers=("F.Fab", "B.Fab"), stype="dash")
    # The same envelope on silk, so the printed board shows how far a plugged-in
    # board reaches: as wide as the Ra-02 breakout and as high as the E07's edge,
    # i.e. the worst case of the three.  Its top edge breaks around the socket
    # box and its left edge around R1's pads (the Ra-02 overhangs both).
    ko_x0, ko_x1, ko_y, ko_end = mx - RA02_W / 2, mx + RA02_W / 2, SY0 - E07_ROW_IN, CC_H - 0.5
    c.silk_gapped("ko_top", (ko_x0, ko_y), (ko_x1, ko_y), [(sx(7) - 1.3, SY0 - 1.3, sx(1) + 1.3, SY1 + 1.3)], clear=0.5)
    c.silk_gapped("ko_left", (ko_x0, ko_y), (ko_x0, ko_end), [(R1_X - 0.7, R1_Y + dy - 0.6, R1_X + 0.7, R1_Y + dy + 0.6) for dy in (-1.0, 1.0)])
    c.silk_gapped("ko_right", (ko_x1, ko_y), (ko_x1, ko_end), [])
    c.silk("sockname", "E07-M1101D / D-Sun / Ra-02", mx, CC_H - 0.9, 0.6)
    for i, net in enumerate(EXP_PINS, 1):  # the UART pins carry their function too (21TX, 20RX)
        c.silk(f"exp{i}", EXP_LABELS[net] + EXP_UART.get(net, ""), ex(i), EXP_Y - 1.3, 0.5)
    c.silk("jp1", "RA-02", JP1_X + 0.5, JP1_Y - 1.7, 0.5)
    c.silk("j5_1", "21", J5_X, J5_Y + 1.45, 0.5)  # below the pads: the gap above them carries J1's pin names
    c.silk("j5_2", "20 DIO2", J5_X + SM_PITCH, J5_Y + 1.45, 0.5)
    c.title_silk("ESP32-C3 + CC1101 / Ra-02 433MHz")
    return c.d


def main() -> None:
    ap = argparse.ArgumentParser(description=__doc__, formatter_class=argparse.RawDescriptionHelpFormatter)
    ap.add_argument("--out", type=pathlib.Path, default=pathlib.Path(__file__).resolve().parent.parent / "hardware")
    args = ap.parse_args()
    for d in (build_sx1278(), build_radio()):
        d.write(args.out / d.project)


if __name__ == "__main__":
    main()
