mithro/esp32-to-433mhz/firmware/tools/cc1101.py

"""Minimal CC1101 driver — just enough for FSK receive at user-specified params.

Datasheet reference: TI CC1101 SWRS061I.
Designed to run on the Raspberry Pi 5 over /dev/spidev0.0.
"""
from __future__ import annotations

import spidev
import time

# ── Command strobes (single-byte writes, no data follows) ────────────
SRES   = 0x30  # Reset chip
SFSTXON = 0x31 # Enable + calibrate frequency synth
SCAL   = 0x33  # Calibrate frequency synth and turn off
SRX    = 0x34  # Enable RX
STX    = 0x35  # Enable TX
SIDLE  = 0x36  # Exit RX/TX, turn off frequency synth
SFRX   = 0x3A  # Flush RX FIFO (only in IDLE / RXFIFO_OVERFLOW)
SFTX   = 0x3B  # Flush TX FIFO (only in IDLE / TXFIFO_UNDERFLOW)
SNOP   = 0x3D  # No-op (read status byte)

# ── Status registers (read with READ | BURST) ────────────────────────
PARTNUM    = 0x30
VERSION    = 0x31
RXBYTES    = 0x3B   # bit 7: RXFIFO_OVERFLOW; bits 6-0: byte count
MARCSTATE  = 0x35   # bits 4-0: state machine ID

# ── Config registers (subset used) ────────────────────────────────────
IOCFG2, IOCFG1, IOCFG0 = 0x00, 0x01, 0x02
FIFOTHR                 = 0x03
SYNC1, SYNC0            = 0x04, 0x05
PKTLEN, PKTCTRL1, PKTCTRL0 = 0x06, 0x07, 0x08
ADDR, CHANNR            = 0x09, 0x0A
FSCTRL1, FSCTRL0        = 0x0B, 0x0C
FREQ2, FREQ1, FREQ0     = 0x0D, 0x0E, 0x0F
MDMCFG4, MDMCFG3, MDMCFG2, MDMCFG1, MDMCFG0 = 0x10, 0x11, 0x12, 0x13, 0x14
DEVIATN                 = 0x15
MCSM2, MCSM1, MCSM0     = 0x16, 0x17, 0x18
FOCCFG, BSCFG           = 0x19, 0x1A
AGCCTRL2, AGCCTRL1, AGCCTRL0 = 0x1B, 0x1C, 0x1D
FREND1, FREND0          = 0x21, 0x22
FSCAL3, FSCAL2, FSCAL1, FSCAL0 = 0x23, 0x24, 0x25, 0x26
TEST2, TEST1, TEST0     = 0x2C, 0x2D, 0x2E
PATABLE                 = 0x3E    # power amplifier table (single-byte access)

# ── FIFO ──────────────────────────────────────────────────────────────
FIFO_ADDR = 0x3F          # FIFO_W = 0x3F; FIFO_R = 0xFF (READ|BURST|0x3F)

# ── SPI access flags ──────────────────────────────────────────────────
READ  = 0x80
BURST = 0x40

# ── MARCSTATE values (just the few we care about) ────────────────────
MARC_IDLE     = 0x01
MARC_RX       = 0x0D
MARC_RXFIFO_OVERFLOW = 0x11


class CC1101:
    def __init__(self, bus: int = 0, device: int = 0, spi_hz: int = 500_000):
        self.spi = spidev.SpiDev()
        self.spi.open(bus, device)
        self.spi.max_speed_hz = spi_hz
        self.spi.mode = 0
        self._last_status = 0

    # ── Low-level SPI ops ────────────────────────────────────────────
    def strobe(self, cmd: int) -> int:
        self._last_status = self.spi.xfer2([cmd])[0]
        return self._last_status

    def write_reg(self, addr: int, value: int) -> None:
        self.spi.xfer2([addr & 0x3F, value & 0xFF])

    def write_burst(self, addr: int, values: list[int]) -> None:
        self.spi.xfer2([(addr & 0x3F) | BURST] + list(values))

    def read_reg(self, addr: int) -> int:
        # Config registers (< 0x30) are read with READ bit only
        return self.spi.xfer2([(addr & 0x3F) | READ, 0x00])[1]

    def read_status(self, addr: int) -> int:
        # Status registers (≥ 0x30) require READ | BURST or you get the
        # config register at the same address instead.
        return self.spi.xfer2([(addr & 0x3F) | READ | BURST, 0x00])[1]

    def read_burst(self, addr: int, n: int) -> list[int]:
        return self.spi.xfer2([(addr & 0x3F) | READ | BURST] + [0] * n)[1:]

    def read_fifo(self, n: int) -> list[int]:
        # FIFO reads use single-byte access for n=1, burst for n>1.
        return self.spi.xfer2([FIFO_ADDR | READ | BURST] + [0] * n)[1:]

    # ── High-level helpers ───────────────────────────────────────────
    def reset(self) -> None:
        self.strobe(SRES)
        time.sleep(0.05)
        # After reset, wait until CHIP_RDY (status byte bit 7 = 0)
        for _ in range(100):
            s = self.strobe(SNOP)
            if not (s & 0x80):
                return
            time.sleep(0.001)
        raise RuntimeError("CC1101 chip never became ready after reset")

    def get_marcstate(self) -> int:
        return self.read_status(MARCSTATE) & 0x1F

    def get_rxbytes(self) -> tuple[int, bool]:
        v = self.read_status(RXBYTES)
        return v & 0x7F, bool(v & 0x80)  # (count, overflow_flag)

    def enable_rx(self) -> None:
        self.strobe(SIDLE)
        self.strobe(SFRX)         # flush RX FIFO
        self.strobe(SCAL)
        time.sleep(0.01)          # calibration ~720 µs
        self.strobe(SRX)

    def transmit(self, payload: bytes) -> None:
        """Transmit a fixed-length payload using current configuration.
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
